trygvis/Quansheng_UV-K5_Wiki/frog-5030712_640.png

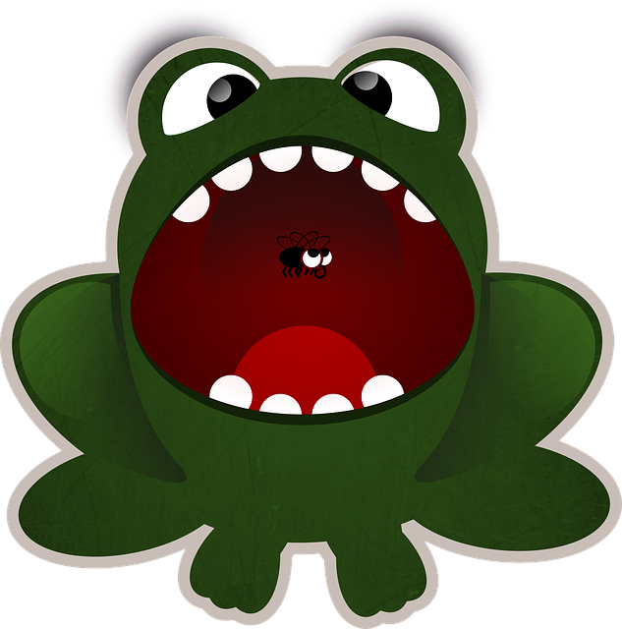
frog-5030712_640.png
