trygvis/Quansheng_UV-K5_Wiki/hardware/Empty_PCB_V1.4/PCB_1.4_FS_2023-09-14 15.27.33.jpg

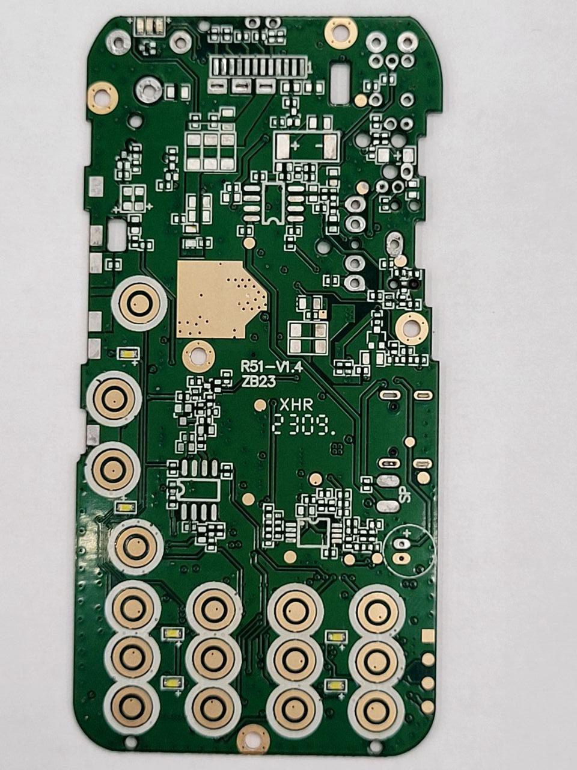
hardware/Empty_PCB_V1.4/PCB_1.4_FS_2023-09-14 15.27.33.jpg
