trygvis/Quansheng_UV-K5_Wiki/hardware/X-Ray/sloping/bok2-5.jpg

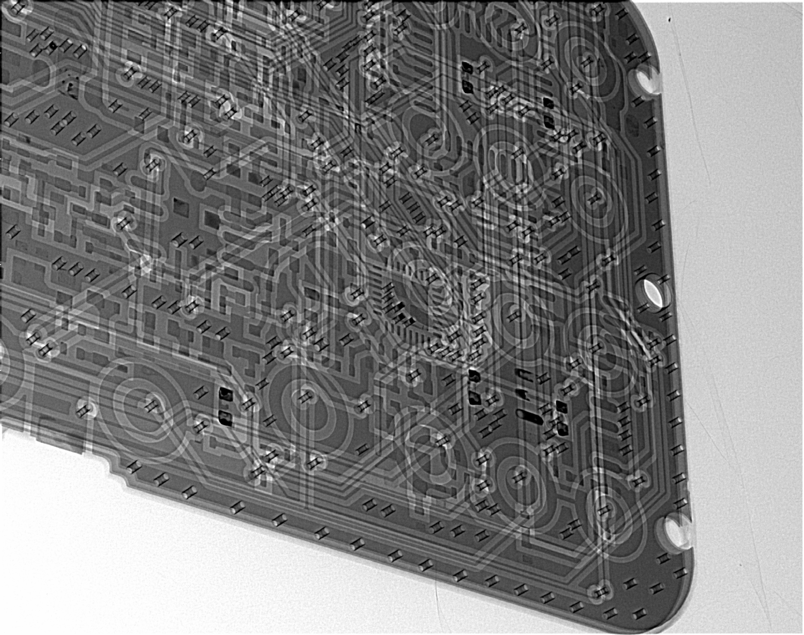
hardware/X-Ray/sloping/bok2-5.jpg
