trygvis/Quansheng_UV-K5_Wiki/hardware/X-Ray/sloping/bok2.jpg

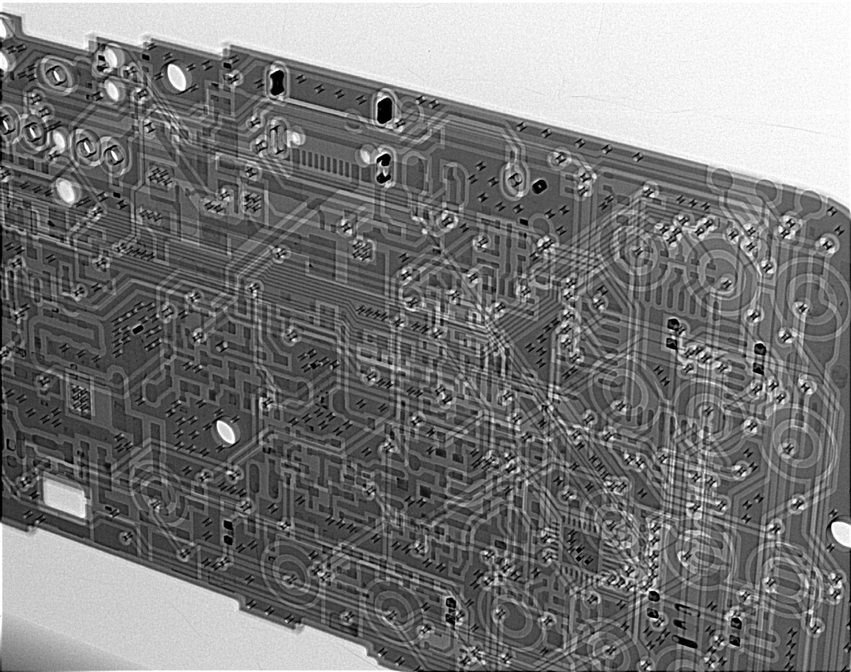
hardware/X-Ray/sloping/bok2.jpg
