trygvis/Quansheng_UV-K5_Wiki/hardware/X-Ray/sloping/bok3.jpg

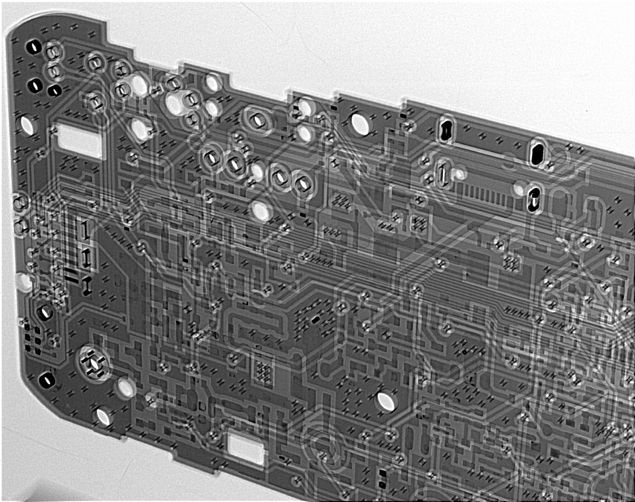
hardware/X-Ray/sloping/bok3.jpg
