trygvis/Quansheng_UV-K5_Wiki/hardware/X-Ray/sloping/bokv2-1.jpg

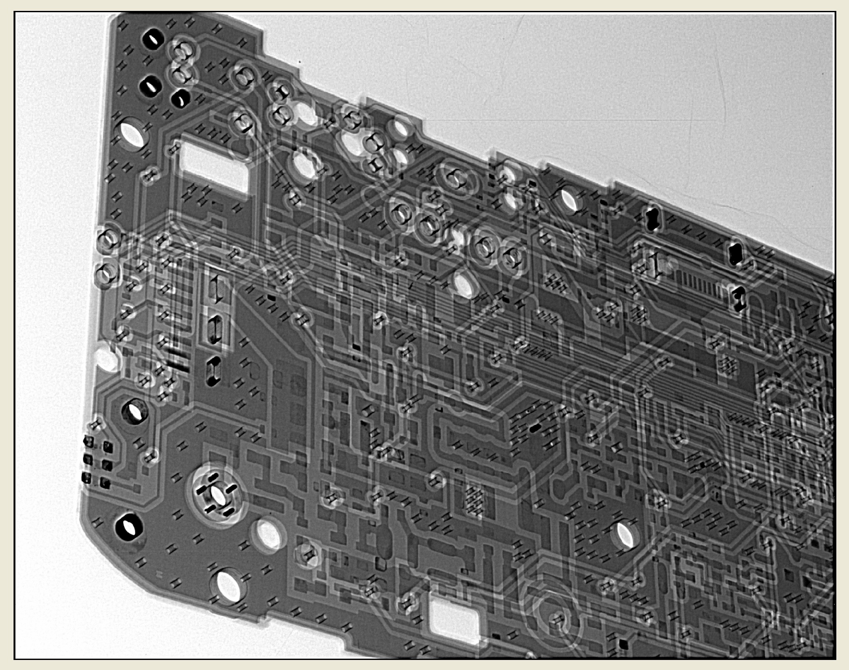
hardware/X-Ray/sloping/bokv2-1.jpg
