trygvis/Quansheng_UV-K5_Wiki/hardware/X-Ray/XRay_RU1_2023-09-13.jpg

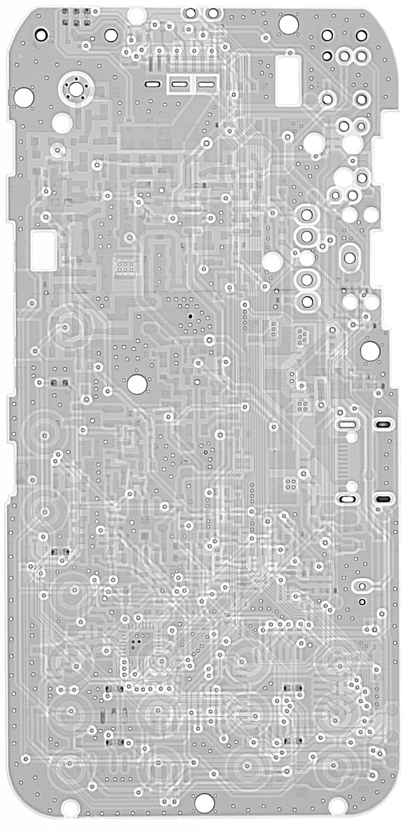
hardware/X-Ray/XRay_RU1_2023-09-13.jpg
