trygvis/Quansheng_UV-K5_Wiki/Manual/Custom_Bootloader_with_Multiple_Firmwares_on_Quansheng_UV_K5_UV.pdf

## Custom Bootloader with Multiple Firmwares on Quansheng UV-K5 UV-K6

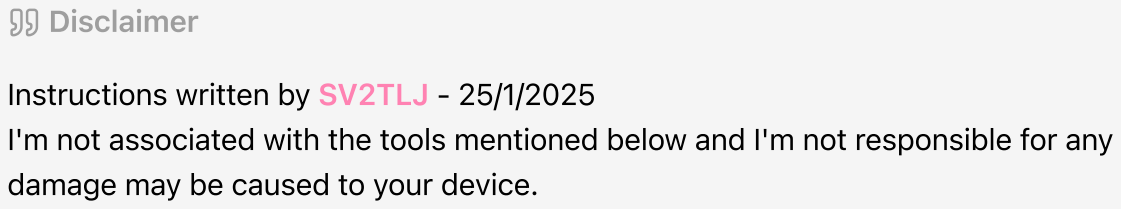
[picture p77: figure]
Disclaimer; damage may be caused to your device.

This method allows us to store up to 4 firmwares in EEPROM and select which one to flash on the go. The selection is done through a list menu and allows us to switch between firmwares without a computer.

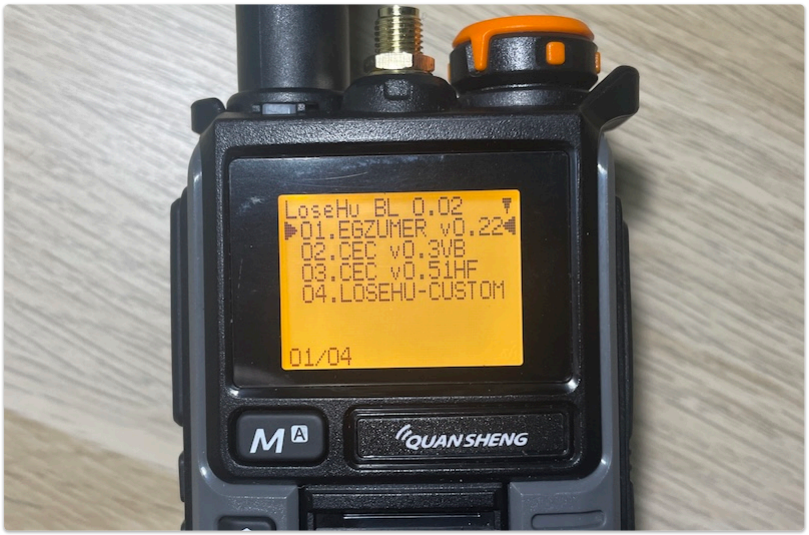
[picture p78: figure]

You will need:

Instructions written by SV2TLJ - 25/1/2025
I'm not associated with the tools mentioned below and I'm not responsible for any

2x 2Mib EEPROM chips (M24M02, AT24CM02, BL24CM02A) Soldering Iron
ST-Link and four wires with female Dupont
Chrome based browser

## Install EEPROM

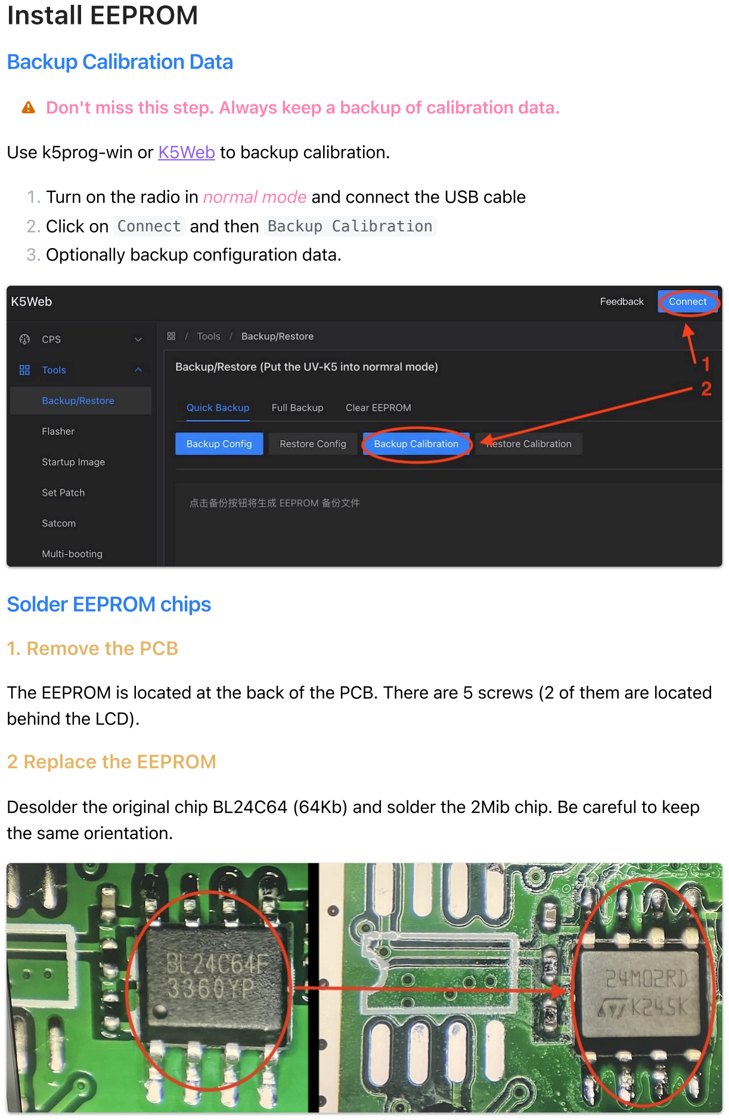
[picture p79: page 2]

Backup Calibration Data

Use k5prog-win or K5Web (https://k5.vicicode.com/#/tool/backup) to backup calibration.

Solder EEPROM chips

1. Remove the PCB

The EEPROM is located at the back of the PCB. There are 5 screws (2 of them are located behind the LCD).

2 Replace the EEPROM

Desolder the original chip BL24C64 (64Kb) and solder the 2Mib chip. Be careful to keep the same orientation.

Don't miss this step. Always keep a backup of calibration data.

1. Turn on the radio in normal mode and connect the USB cable
2. Click on Connect and then Backup Calibration
3. Optionally backup configuration data.

3. Add the second EEPROM

The radio I modded is a UV-K5(99) and it came with a PCB version R51-V1.8. On this PCB there is already a populated footprint for another EEPROM.

For other PCB versions:
If there is not a location to solder the 2nd chip, you need to solder jumper wires between the two chips. Connect all the pads of the two chips in parallel (pad 1 to pad1, pad 2 to pad 2 e.t.c), except pad 3.
Pad 3 on the 1st EEPROM is connected to ground. Pad 3 on the 2nd EEPROM should be pulled up to Vcc. Put a jumper or a 10K resistor between pad 3 and pad 8 on the 2nd chip.

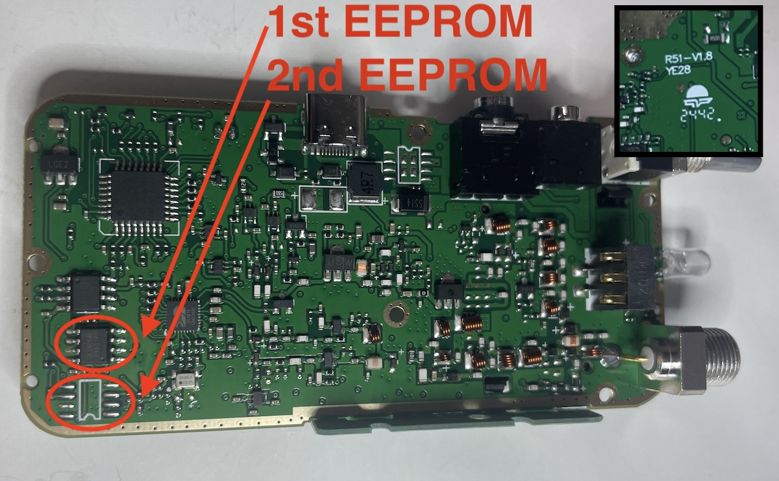
[picture p80: figure]

## Bootloader with multiple firmwares

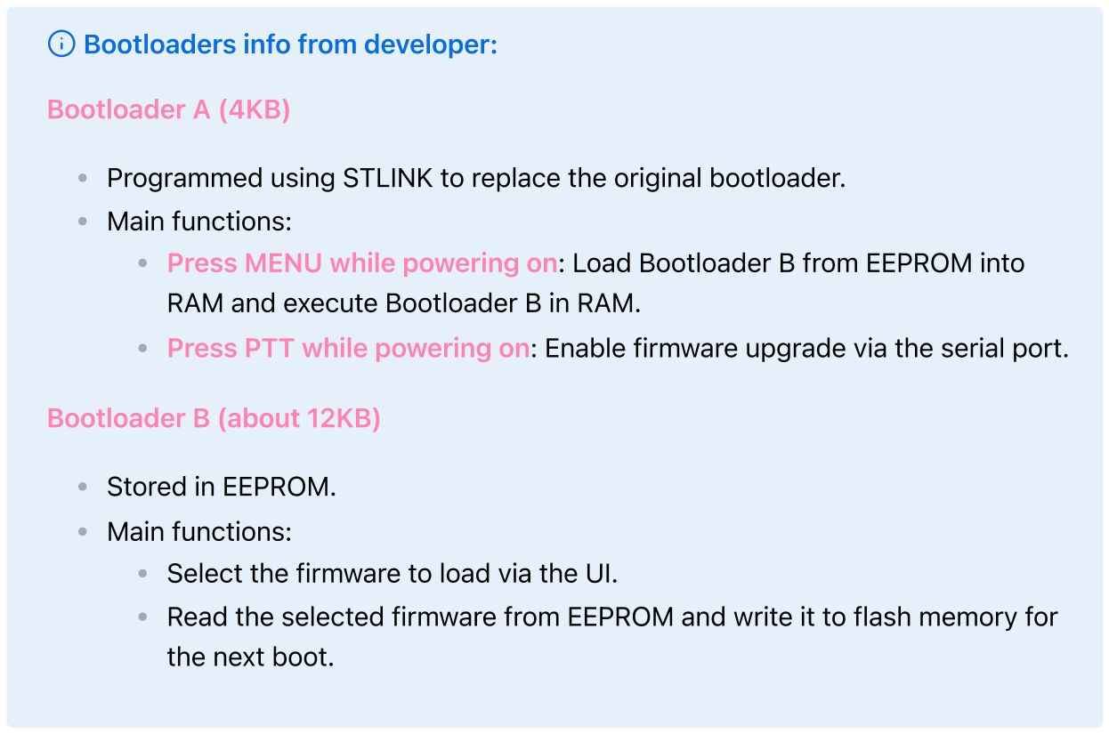
[picture p81: figure]
Bootloaders info from developer:; Bootloader A (4KB); Bootloader B (about 12KB); Main functions:; RAM and execute Bootloader B in RAM.; Stored in EEPROM. Main functions: Select the firmware to load via the UI.; the next boot.

1. Flash the losehu firmware

Go to LOSEHU DIY (https://k5.vicicode.com/#/idea/losehu) and select the Chinese Channel Name . This firmware requires a 4Mib EEPROM installed and its name ends with 400000000 .

Programmed using STLINK to replace the original bootloader.

Press MENU while powering on: Load Bootloader B from EEPROM into

Press PTT while powering on: Enable firmware upgrade via the serial port.

Read the selected firmware from EEPROM and write it to flash memory for

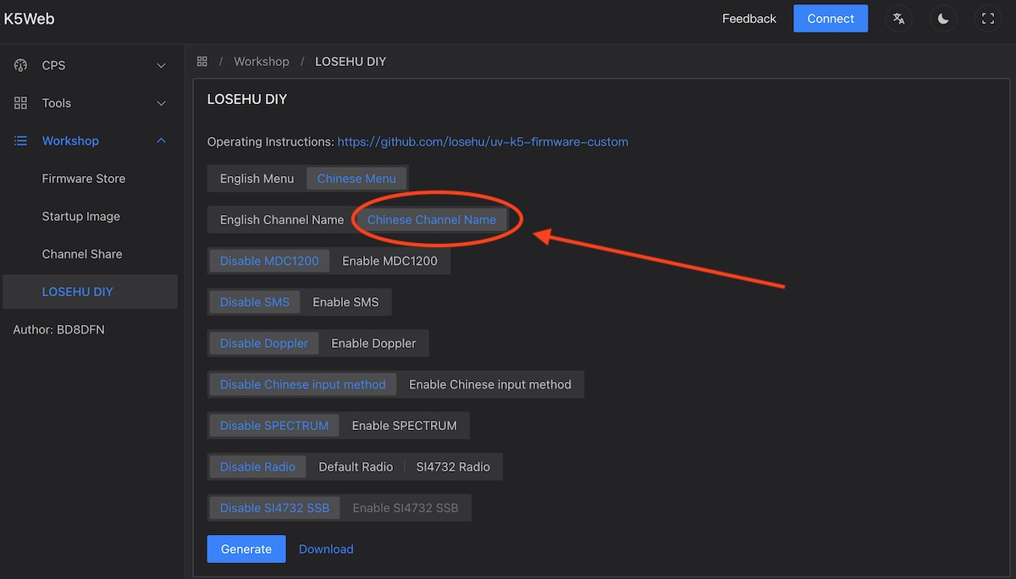
[picture p82: figure]
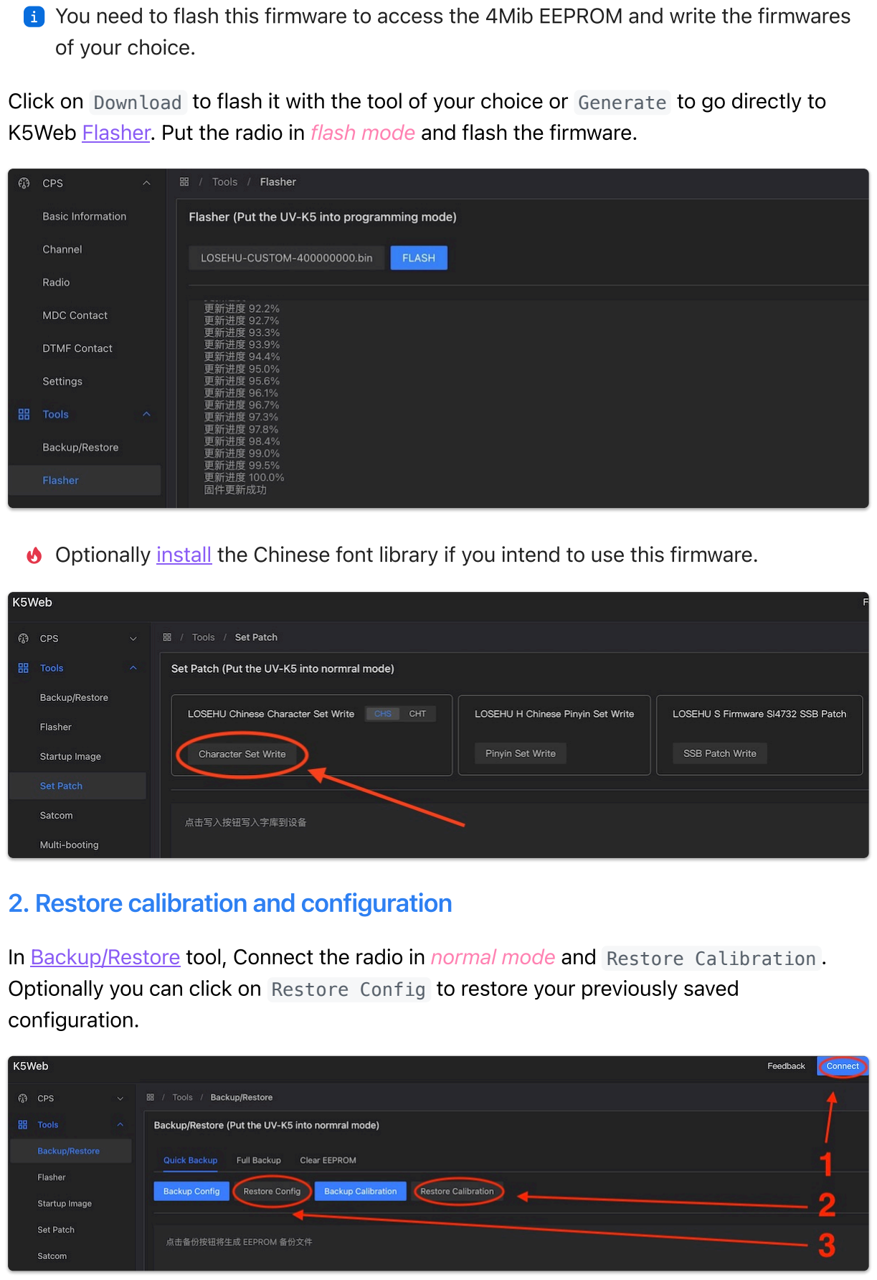
[picture p83: page 5]

Click on Download to flash it with the tool of your choice or Generate to go directly to K5Web Flasher. (https://k5.vicicode.com/#/tool/flash) Put the radio in flash mode and flash the firmware.

2. Restore calibration and configuration

In Backup/Restore (https://k5.vicicode.com/#/tool/backup) tool, Connect the radio in normal mode and Restore Calibration . Optionally you can click on Restore Config to restore your previously saved configuration.

You need to flash this firmware to access the 4Mib EEPROM and write the firmwares of your choice.

Optionally install (https://k5.vicicode.com/#/tool/chi) the Chinese font library if you intend to use this firmware.

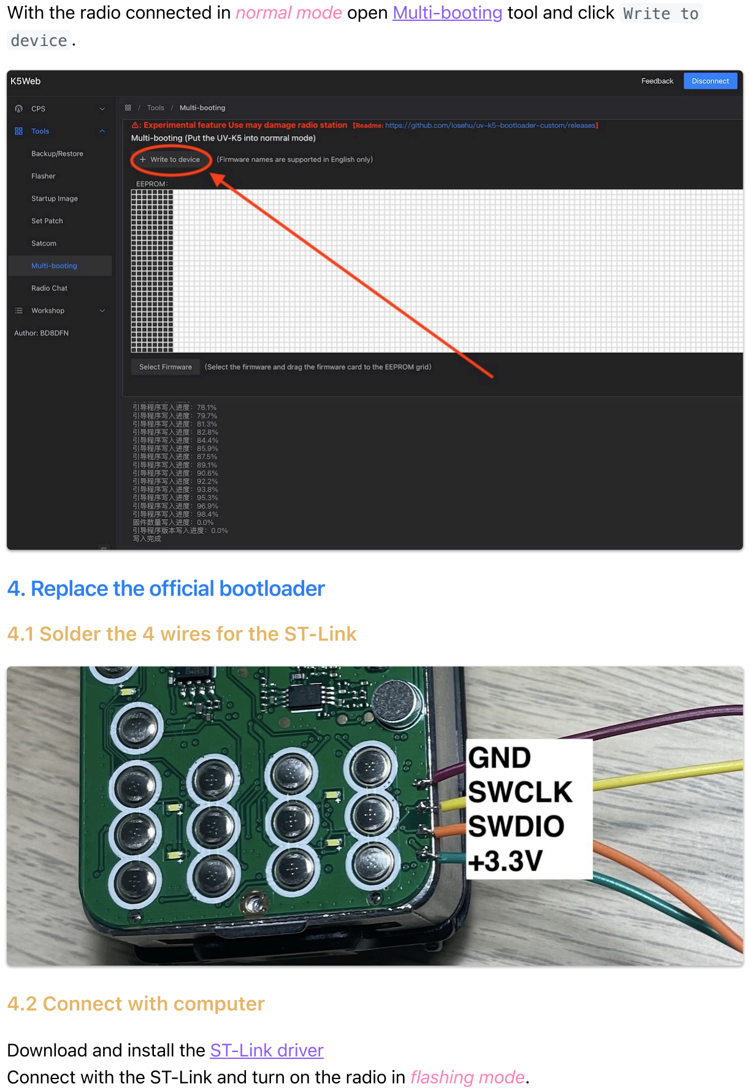
[picture p84: page 6]

With the radio connected in normal mode open Multi-booting (https://k5.vicicode.com/#/tool/bl) tool and click Write to
device .
4. Replace the official bootloader

4.1 Solder the 4 wires for the ST-Link

4.2 Connect with computer

Download and install the ST-Link driver (https://www.st.com/en/development-tools/stsw-link009.html)
Connect with the ST-Link and turn on the radio in flashing mode.

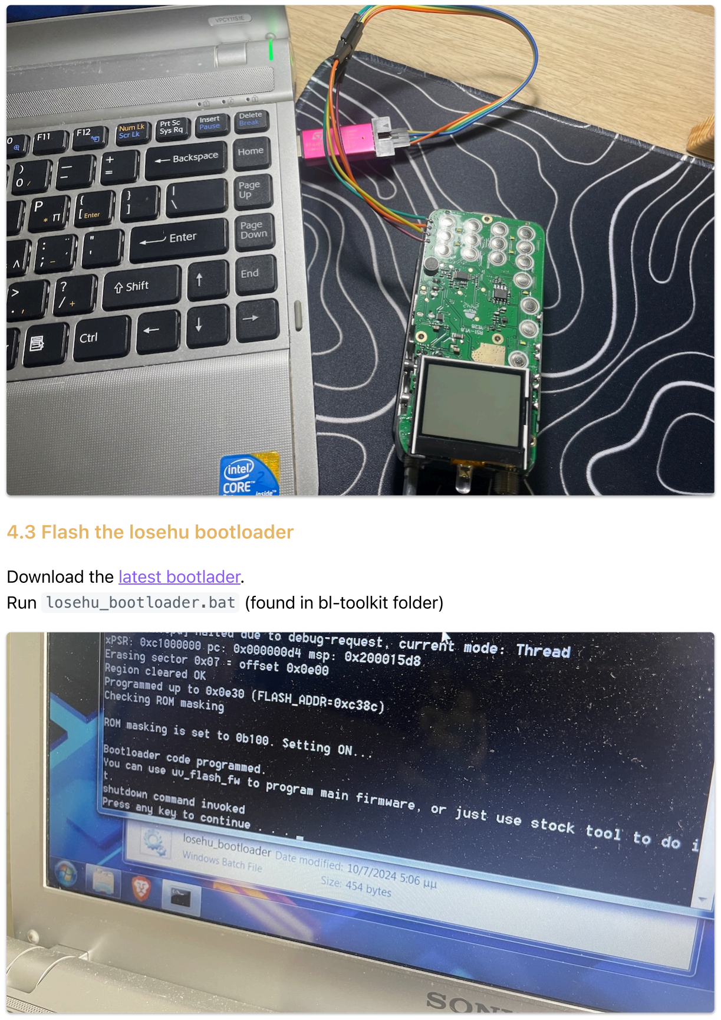
[picture p85: page 7]

4.3 Flash the losehu bootloader

Download the latest bootlader. (https://github.com/losehu/uv-k5-bootloader-custom/releases)
Run losehu_bootloader.bat (found in bl-toolkit folder)

5. Write firmware in EEPROM

Use Multi-booting (https://k5.vicicode.com/#/tool/bl) tool with the radio connected in normal mode.
Click Select Firmare and open the firmwares you want to write (up to 4 files). Drag each one on the first white square.
Click Write to device to write all of them.

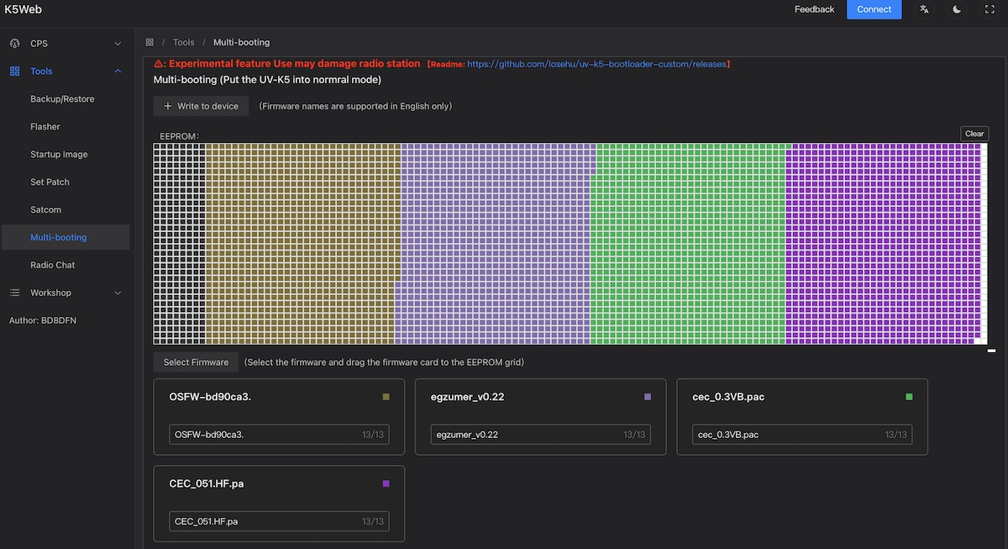
[picture p86: figure]

6. Testflashing using EEPROM

Turn on the radio with the Menu button pressed. You should see a list of the installed firmwares in EEPROM. Select you choice with the arrows and use the Menu button to start flashing. If it stucks for a while and it's not rebooting you might have forgotten to restore the calibration data.

You need to have losehu firmware flashed to use K5Web Multi-Booting tool.

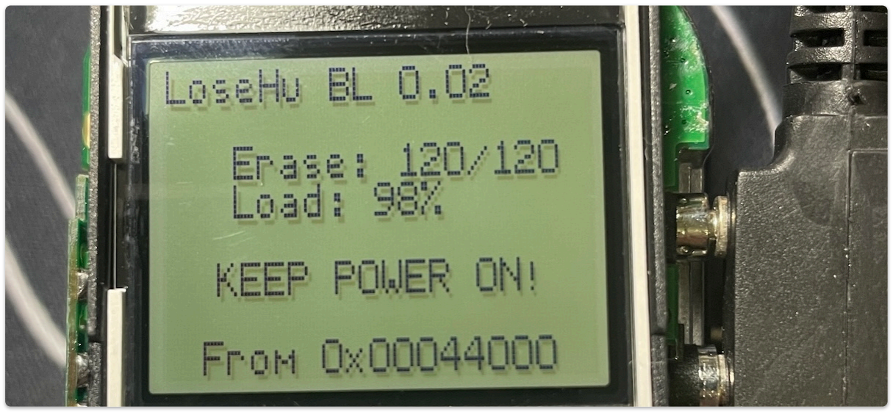
[picture p87: figure]

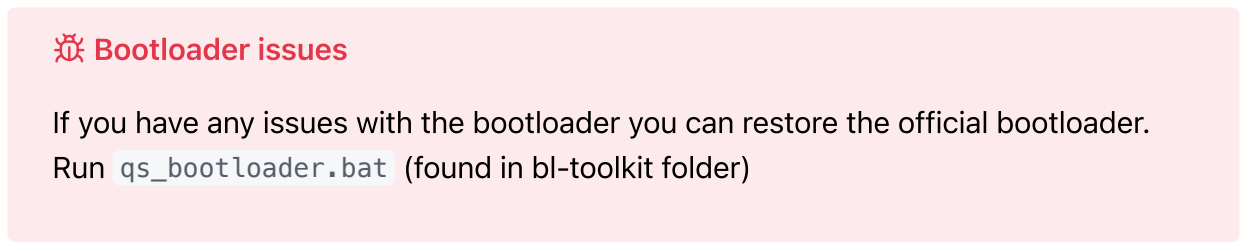
[picture p88: figure]
Bootloader issues

## Useful links

losehu uv-k5-firmware-custom (https://github.com/losehu/uv-k5-firmware-custom) - README en (https://github.com/losehu/uv-k5-firmware-custom/blob/main/README_en.md)
losehu uv-k5-bootloader-custom (https://github.com/losehu/uv-k5-bootloader-custom) - README en (https://github.com/losehu/uv-k5-bootloader-custom/blob/main/README_en.md) - Instructions (https://github.com/losehu/uv-k5-bootloader-custom/blob/main/Losehu%20Bootloader%E8%AF%B4%E6%98%8E%E4%B9%A6.pdf) in Chinese

Tools:

If you have any issues with the bootloader you can restore the official bootloader. Run qs_bootloader.bat (found in bl-toolkit folder)

K5Web (https://k5.vicicode.com/#/chirp/base)
k5prog-win (https://github.com/OneOfEleven/k5prog-win)
