trygvis/Quansheng_UV-K5_Wiki/hardware/Block_Diagram/Quansheng_UV-K5_Block_Diagram_v01.drawio.pdf

~

~~

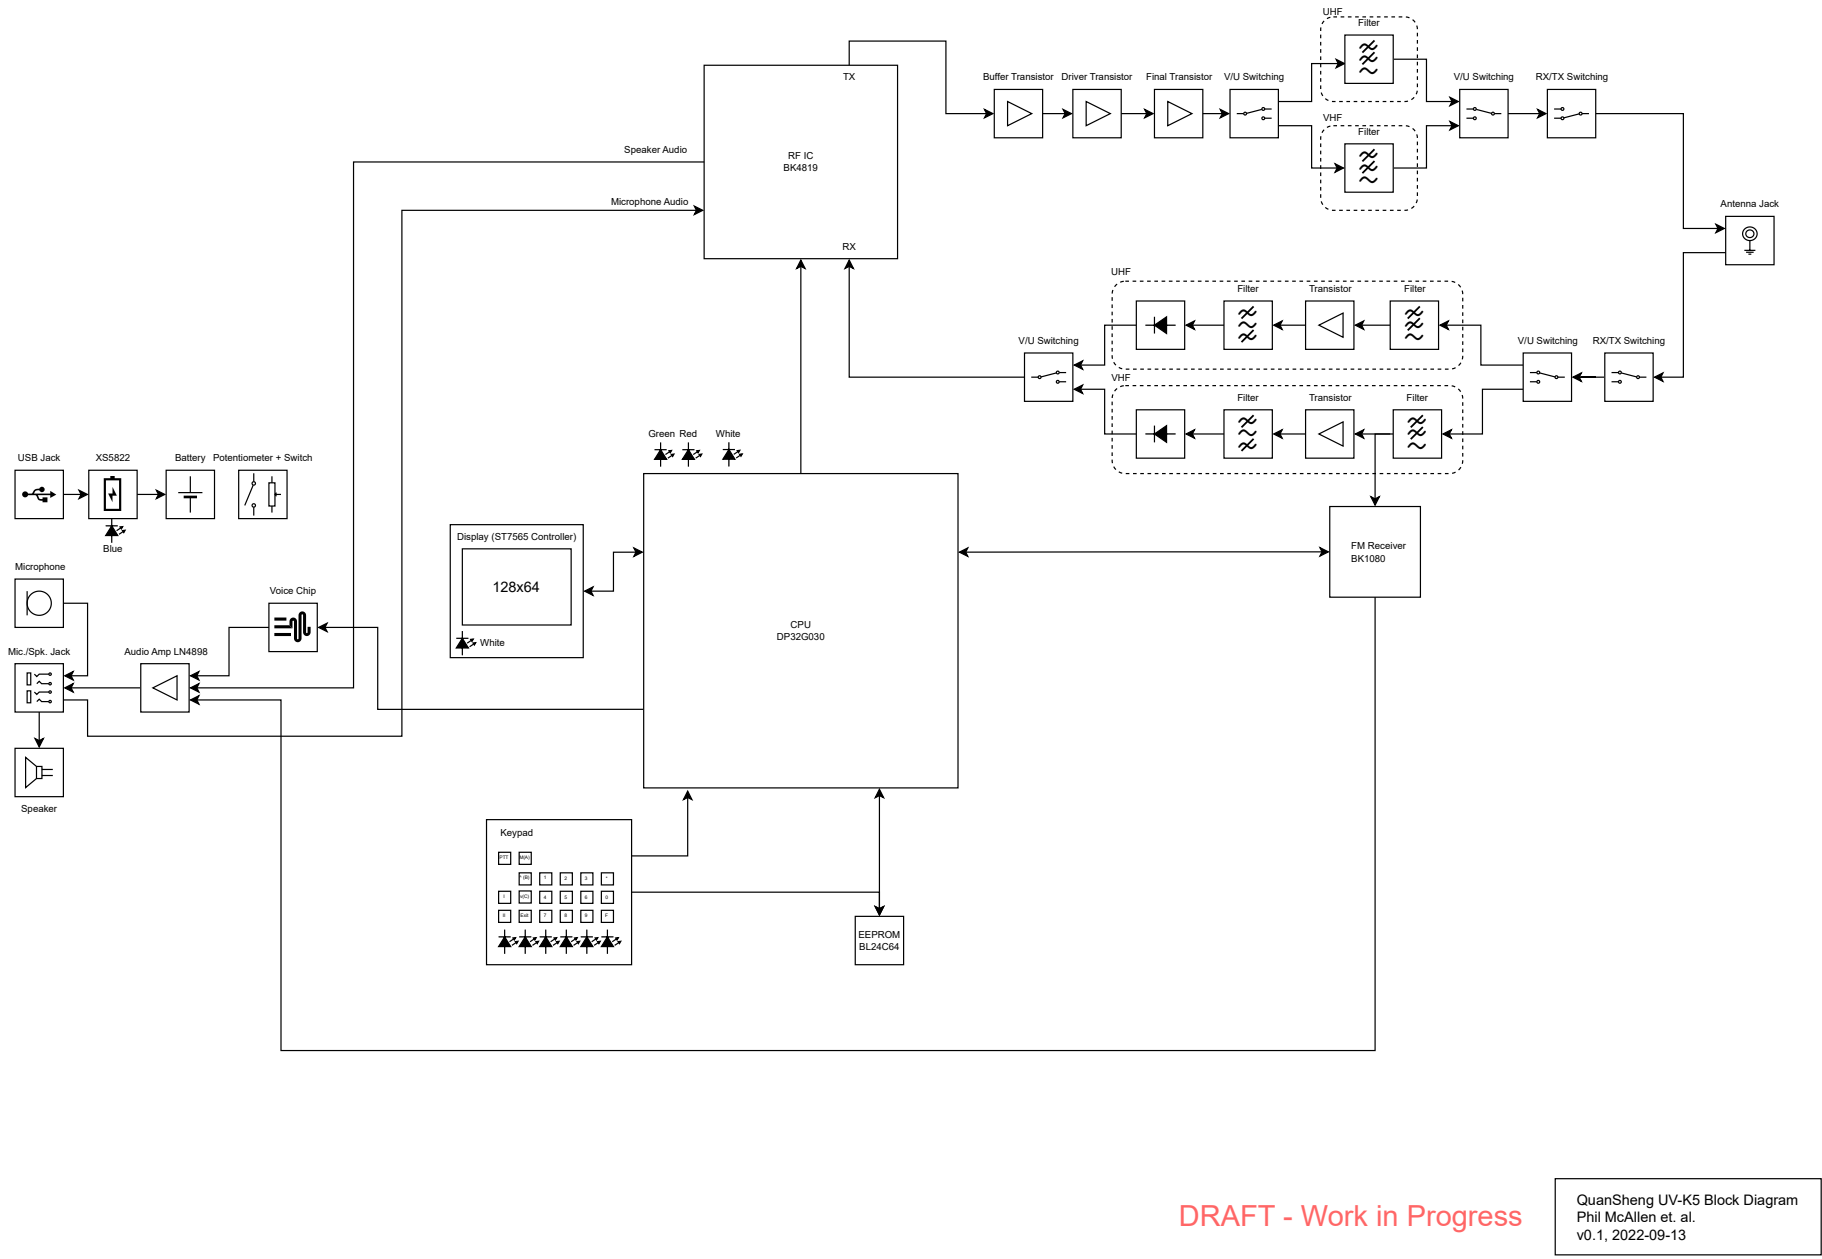
[picture p89: page 1]
Speaker; Antenna Jack; CPU DP32G030; Audio Amp LN4898; Microphone; USB Jack; Keypad; FM Receiver BK1080; EEPROM BL24C64; Voice Chip; Battery; Display (ST7565 Controller); White; Transistor; Buffer Transistor Driver Transistor; Final Transistor; UHF; VHF; V/U Switching; Microphone Audio; Speaker Audio; RX/TX Switching; Potentiometer + Switch; Filter ~~; Filter ~; PTT; Exit; Blue; Green Red; Filter

RX/TX Switching

Mic./Spk. Jack

QuanSheng UV-K5 Block Diagram
Phil McAllen et. al.

DRAFT - Work in Progress
