trygvis/Quansheng_UV-K5_Wiki/hardware/KiCad/UVK5_reversing-70MHz_modv_20230702.pdf

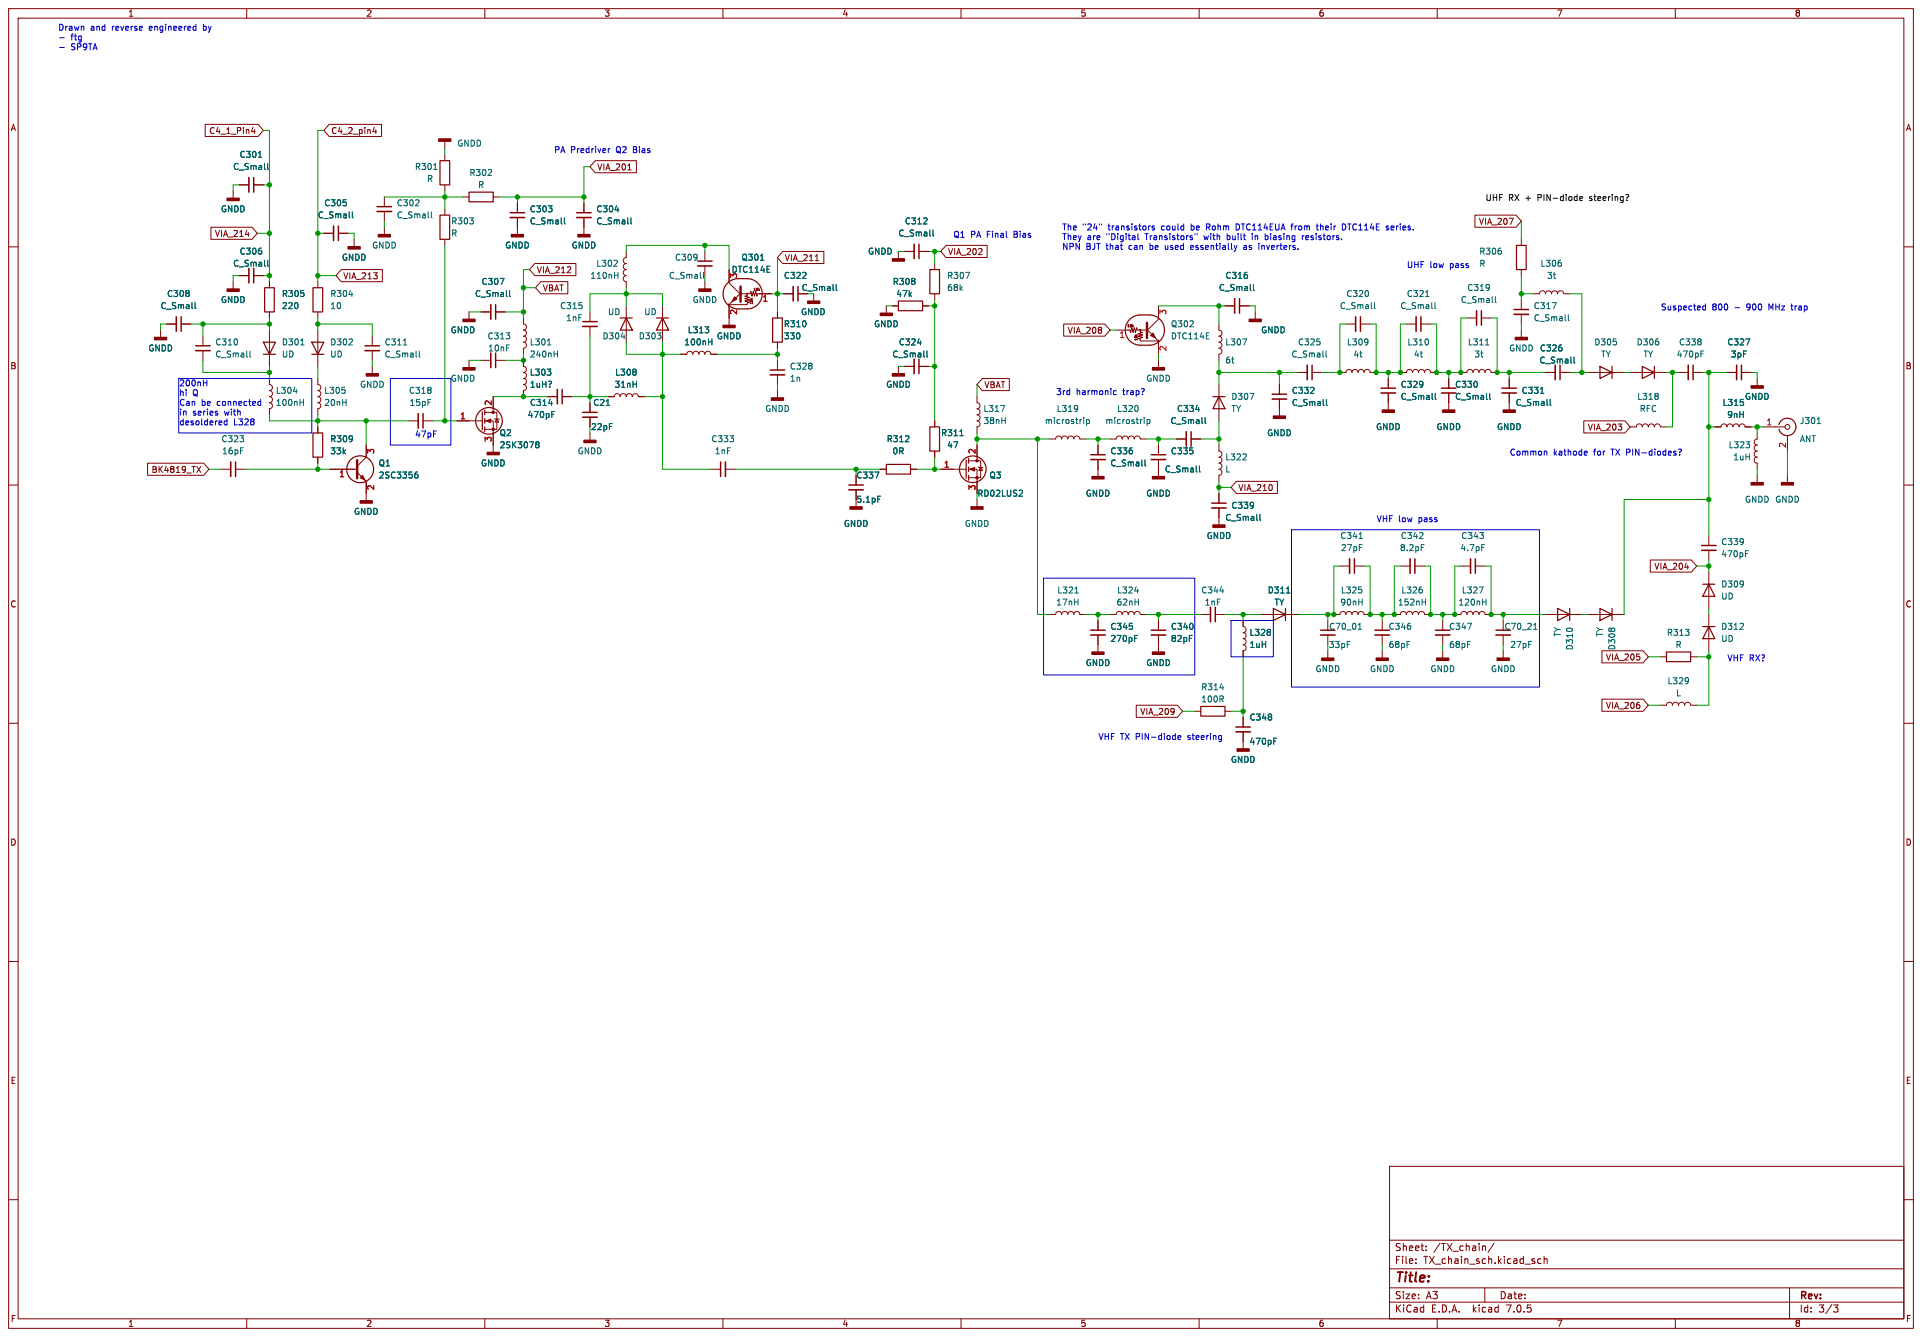
[picture p90: page 1]

Id: 3/3 Title: File: TX_chain_sch.kicad_sch Sheet: /TX_chain/
