trygvis/Quansheng_UV-K5_Wiki/hardware/KiCad/UVK5_reversing_06-02-2024/CPU.kicad_sch

## KiCad design hardware/KiCad/UVK5_reversing_06-02-2024/CPU.kicad_sch (2024-02-06)

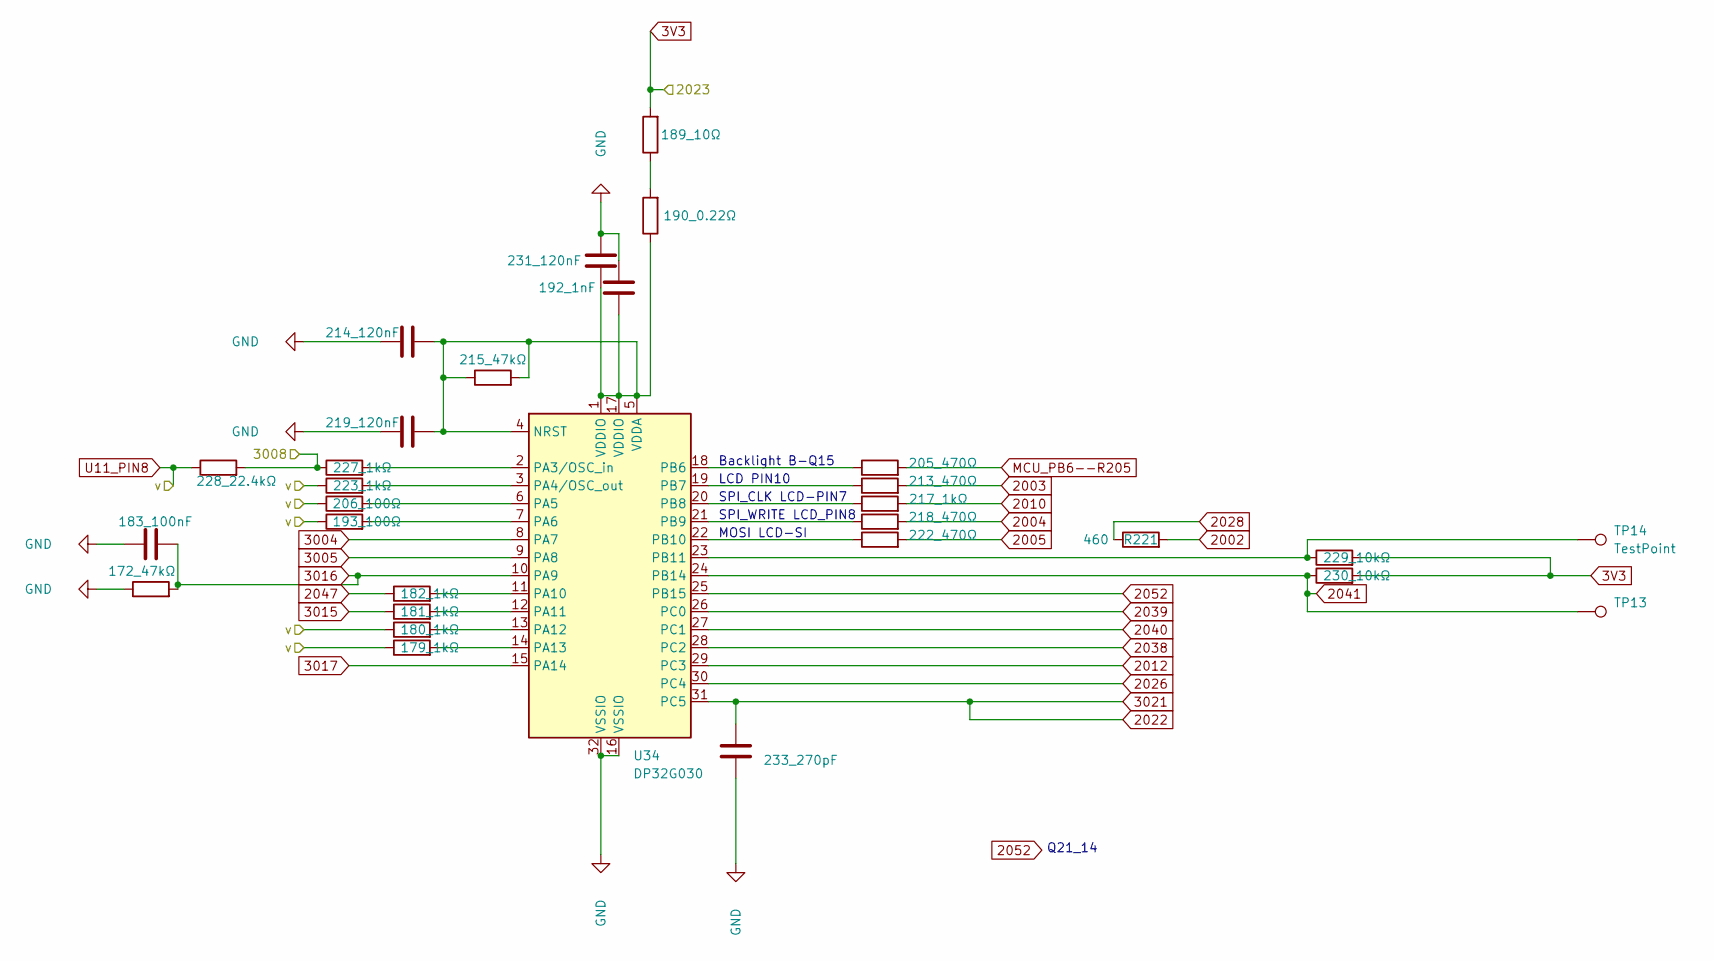
[picture p91: schematic CPU.kicad_sch]

Parts:
C94: 192_1nF
C126: 219_120nF
C183: 183_100nF
C214: 214_120nF
C231: 231_120nF
C233: 233_270pF
R91: 190_0.22Ω
R92: 189_10Ω
R95: 215_47kΩ
R96: 228_22.4kΩ
R97: 180_1kΩ
R100: 179_1kΩ
R172: 172_47kΩ
R181: 181_1kΩ
R182: 182_1kΩ
R193: 193_100Ω
R205: 205_470Ω
R206: 206_100Ω
R213: 213_470Ω
R217: 217_1kΩ
R218: 218_470Ω
R221: 460
R222: 222_470Ω
R223: 223_1kΩ
R227: 227_1kΩ
R229: 229_10kΩ
R230: 230_10kΩ
TP13, TP14: TestPoint
U34: DP32G030; LQFP-32_7x7mm_P0.8mm

Connections:
3V3: R92.2, R229.2, R230.2
2002: R221.2
2003: R213.2
2004: R218.2
2005: R222.2
2010: R217.2
2012: U34.29 (PC3)
2022: C233.2, U34.31 (PC5)
2026: U34.30 (PC4)
2028: R221.1
2038: U34.28 (PC2)
2039: U34.26 (PC0)
2040: U34.27 (PC1)
2041: R230.1, TP13.1, U34.24 (PB14)
2047: R182.1
2052: U34.25 (PB15)
3004: U34.8 (PA7)
3005: U34.9 (PA8)
3008: R96.2, R227.1
3015: R181.1
3016: C183.2, R172.2, U34.10 (PA9)
3017: U34.15 (PA14)
GND: C94.1, C126.1, C183.1, C214.1, C231.1, C233.1, R172.1, U34.16 (VSSIO), U34.32 (VSS)
MCU_PB6--R205: R205.2
unnamed: C94.2, C126.2, C214.2, C231.2, R91.1, R95.1, R95.2, U34.1 (VDDIO), U34.4 (NRST), U34.5 (VDDA), U34.17 (VDDIO)
unnamed: R91.2, R92.1
unnamed: R97.2, U34.13 (PA12)
unnamed: R100.2, U34.14 (PA13)
unnamed: R181.2, U34.12 (PA11)
unnamed: R182.2, U34.11 (PA10)
unnamed: R193.2, U34.7 (PA6)
unnamed: R205.1, U34.18 (PB6)
unnamed: R206.2, U34.6 (PA5)
unnamed: R213.1, U34.19 (PB7)
unnamed: R217.1, U34.20 (PB8)
unnamed: R218.1, U34.21 (PB9)
unnamed: R222.1, U34.22 (PB10)
unnamed: R223.2, U34.3 (PA4/OSC_out)
unnamed: R227.2, U34.2 (PA3/OSC_in)
unnamed: R229.1, TP14.1, U34.23 (PB11)
U11_PIN8: R96.1, R97.1, R100.1, R193.1, R206.1, R223.1

Notes on the sheet:
Q21_14
MOSI LCD-SI
Backlight B-Q15
SPI_WRITE LCD_PIN8
LCD PIN10
SPI_CLK LCD-PIN7
