trygvis/Quansheng_UV-K5_Wiki/hardware/KiCad/UVK5_reversing_06-02-2024/Charger.kicad_sch

## KiCad design hardware/KiCad/UVK5_reversing_06-02-2024/Charger.kicad_sch (2025-08-14, an earlier design)

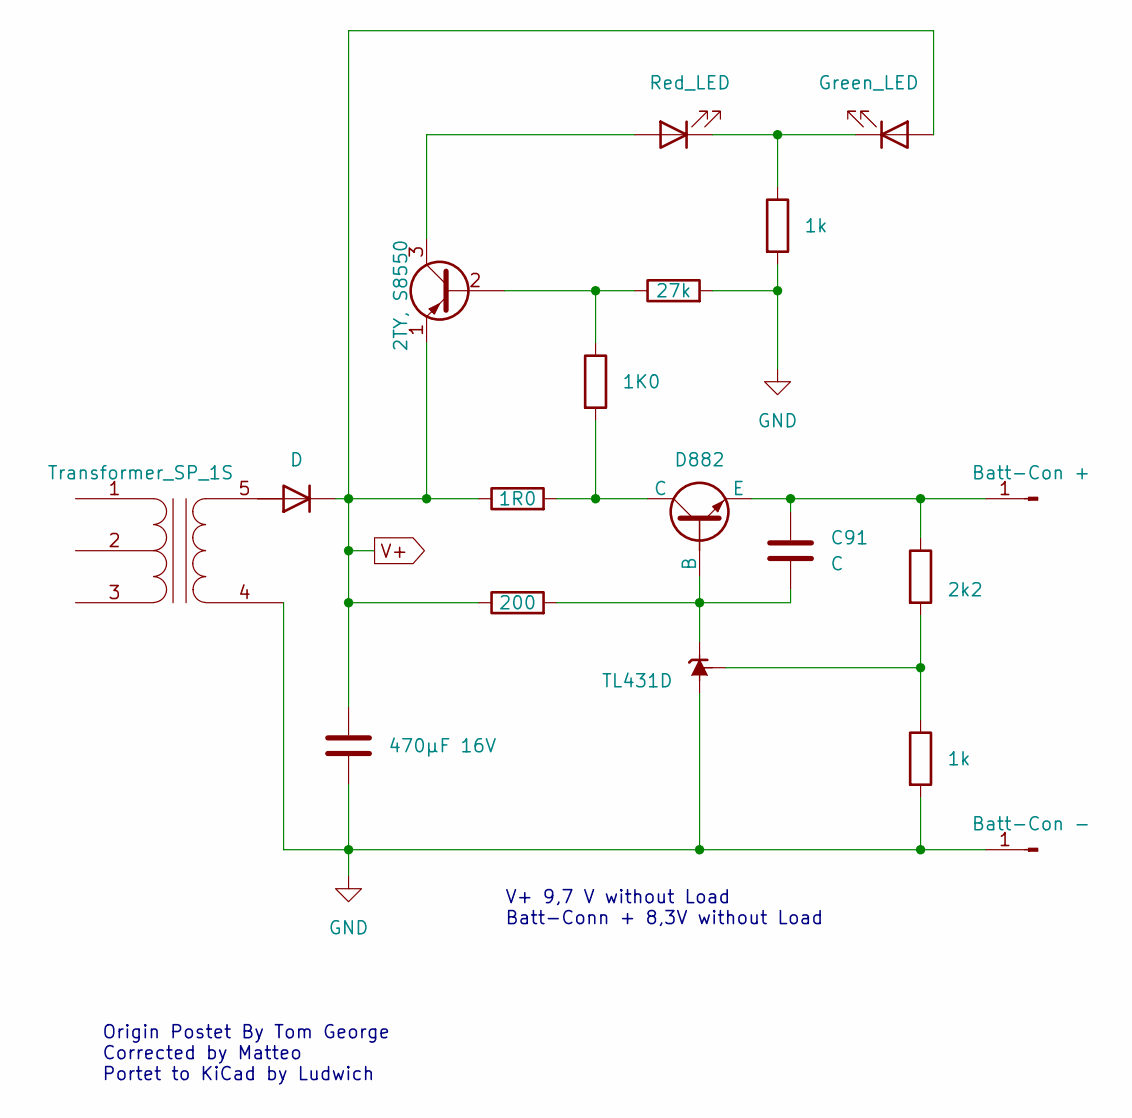
[picture p92: schematic Charger.kicad_sch]

Parts:
C91: C
C92: 470µF 16V
D41: Red_LED
D42: Green_LED
D43: D
J27: Batt-Con +
J28: Batt-Con -
Q30: 2TY, S8550
Q31: D882
R52, R58: 1k
R53: 27k
R55: 1R0
R56: 2k2
R57: 200
T21: Transformer_SP_1S
U23: TL431D; SOIC-8_3.9x4.9mm_P1.27mm
r54: 1K0

Connections:
GND: C92.2, J28.1, R52.2, R53.2, R58.2, T21.4 (S1), U23.2 (A), U23.3 (A), U23.6 (A), U23.7 (A)
unnamed: C91.1, J27.1, Q31.3 (E), R56.1
unnamed: C91.2, Q31.2 (B), R57.2, U23.1 (K)
unnamed: D41.1 (K), D42.1 (K), R52.1
unnamed: D41.2 (A), Q30.3 (C)
unnamed: Q30.2 (B), R53.1, r54.1
unnamed: Q31.1 (C), R55.2, r54.2
unnamed: R56.2, R58.1, U23.8 (REF)
V+: C92.1, D42.2 (A), D43.1 (K), Q30.1 (E), R55.1, R57.1

Notes on the sheet:
V+ 9,7 V without Load Batt-Conn + 8,3V without Load
Origin Postet By Tom George Corrected by Matteo Portet to KiCad by Ludwich
