trygvis/Quansheng_UV-K5_Wiki/hardware/KiCad/UVK5_reversing_06-02-2024/FM_BK1080.kicad_sch

## KiCad design hardware/KiCad/UVK5_reversing_06-02-2024/FM_BK1080.kicad_sch (2024-02-06)

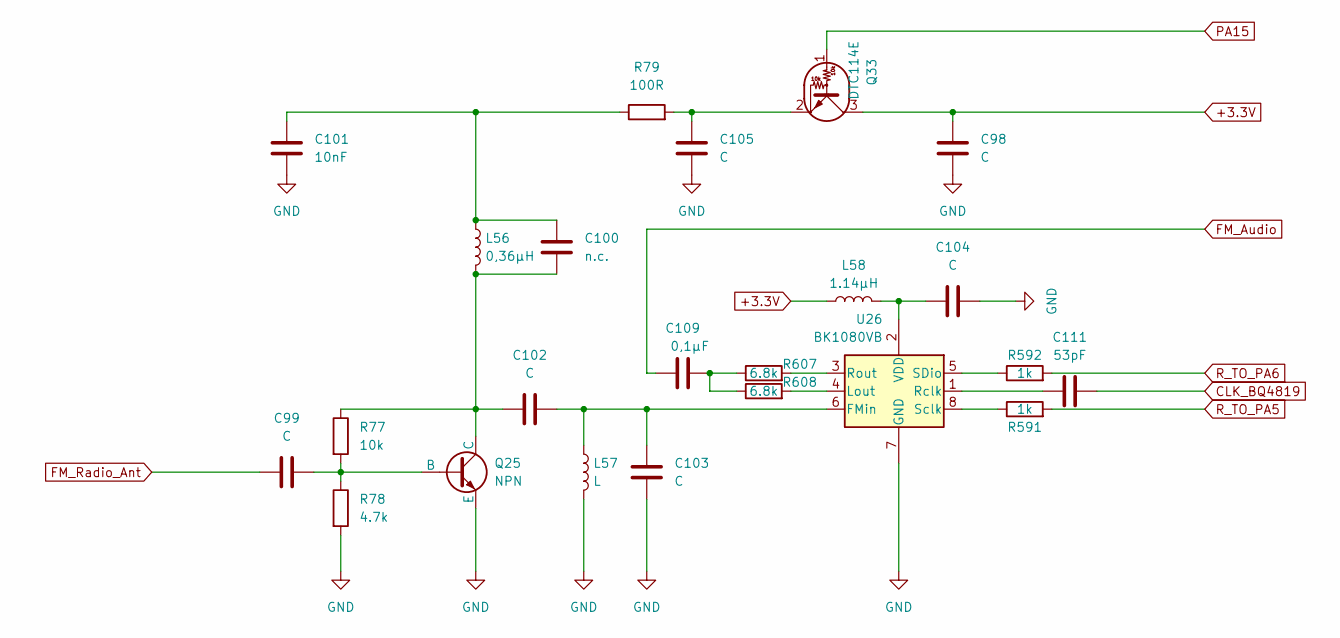
[picture p93: schematic FM_BK1080.kicad_sch]

Parts:
C98, C99, C102, C103, C104, C105: C
C100: n.c.
C101: 10nF
C109: 0,1µF
C111: 53pF
L56: 0,36µH
L57: L
L58: 1.14µH
Q25: NPN
Q33: DTC114E
R77: 10k
R78: 4.7k
R79: 100R
R591, R592: 1k
R607, R608: 6.8k
U26: BK1080VB; SOP-8_3.9x4.9mm_P1.27mm

Connections:
+3.3V: C98.1, L58.1, Q33.3 (C)
CLK_BQ4819: C111.2
FM_Audio: C109.1
FM_Radio_Ant: C99.1
GND: C98.2, C101.2, C103.2, C104.2, C105.2, L57.2, Q25.3 (E), R78.2, U26.7 (GND)
unnamed: C99.2, Q25.2 (B), R77.2, R78.1
unnamed: C100.1, C101.1, L56.1, R79.1
unnamed: C100.2, C102.1, L56.2, Q25.1 (C), R77.1
unnamed: C102.2, C103.1, L57.1, U26.6 (FMin)
unnamed: C104.1, L58.2, U26.2 (VDD)
unnamed: C105.1, Q33.2 (E), R79.2
unnamed: C109.2, R607.1, R608.1
unnamed: C111.1, U26.1 (Rclk)
unnamed: R591.1, U26.8 (Sclk)
unnamed: R592.1, U26.5 (SDio)
unnamed: R607.2, U26.3 (Rout)
unnamed: R608.2, U26.4 (Lout)
PA15: Q33.1 (B)
R_TO_PA5: R591.2
R_TO_PA6: R592.2
