trygvis/Quansheng_UV-K5_Wiki/hardware/KiCad/UVK5_reversing_06-02-2024/Gabiz_ro.kicad_sch

## KiCad design hardware/KiCad/UVK5_reversing_06-02-2024/Gabiz_ro.kicad_sch (2024-02-06)

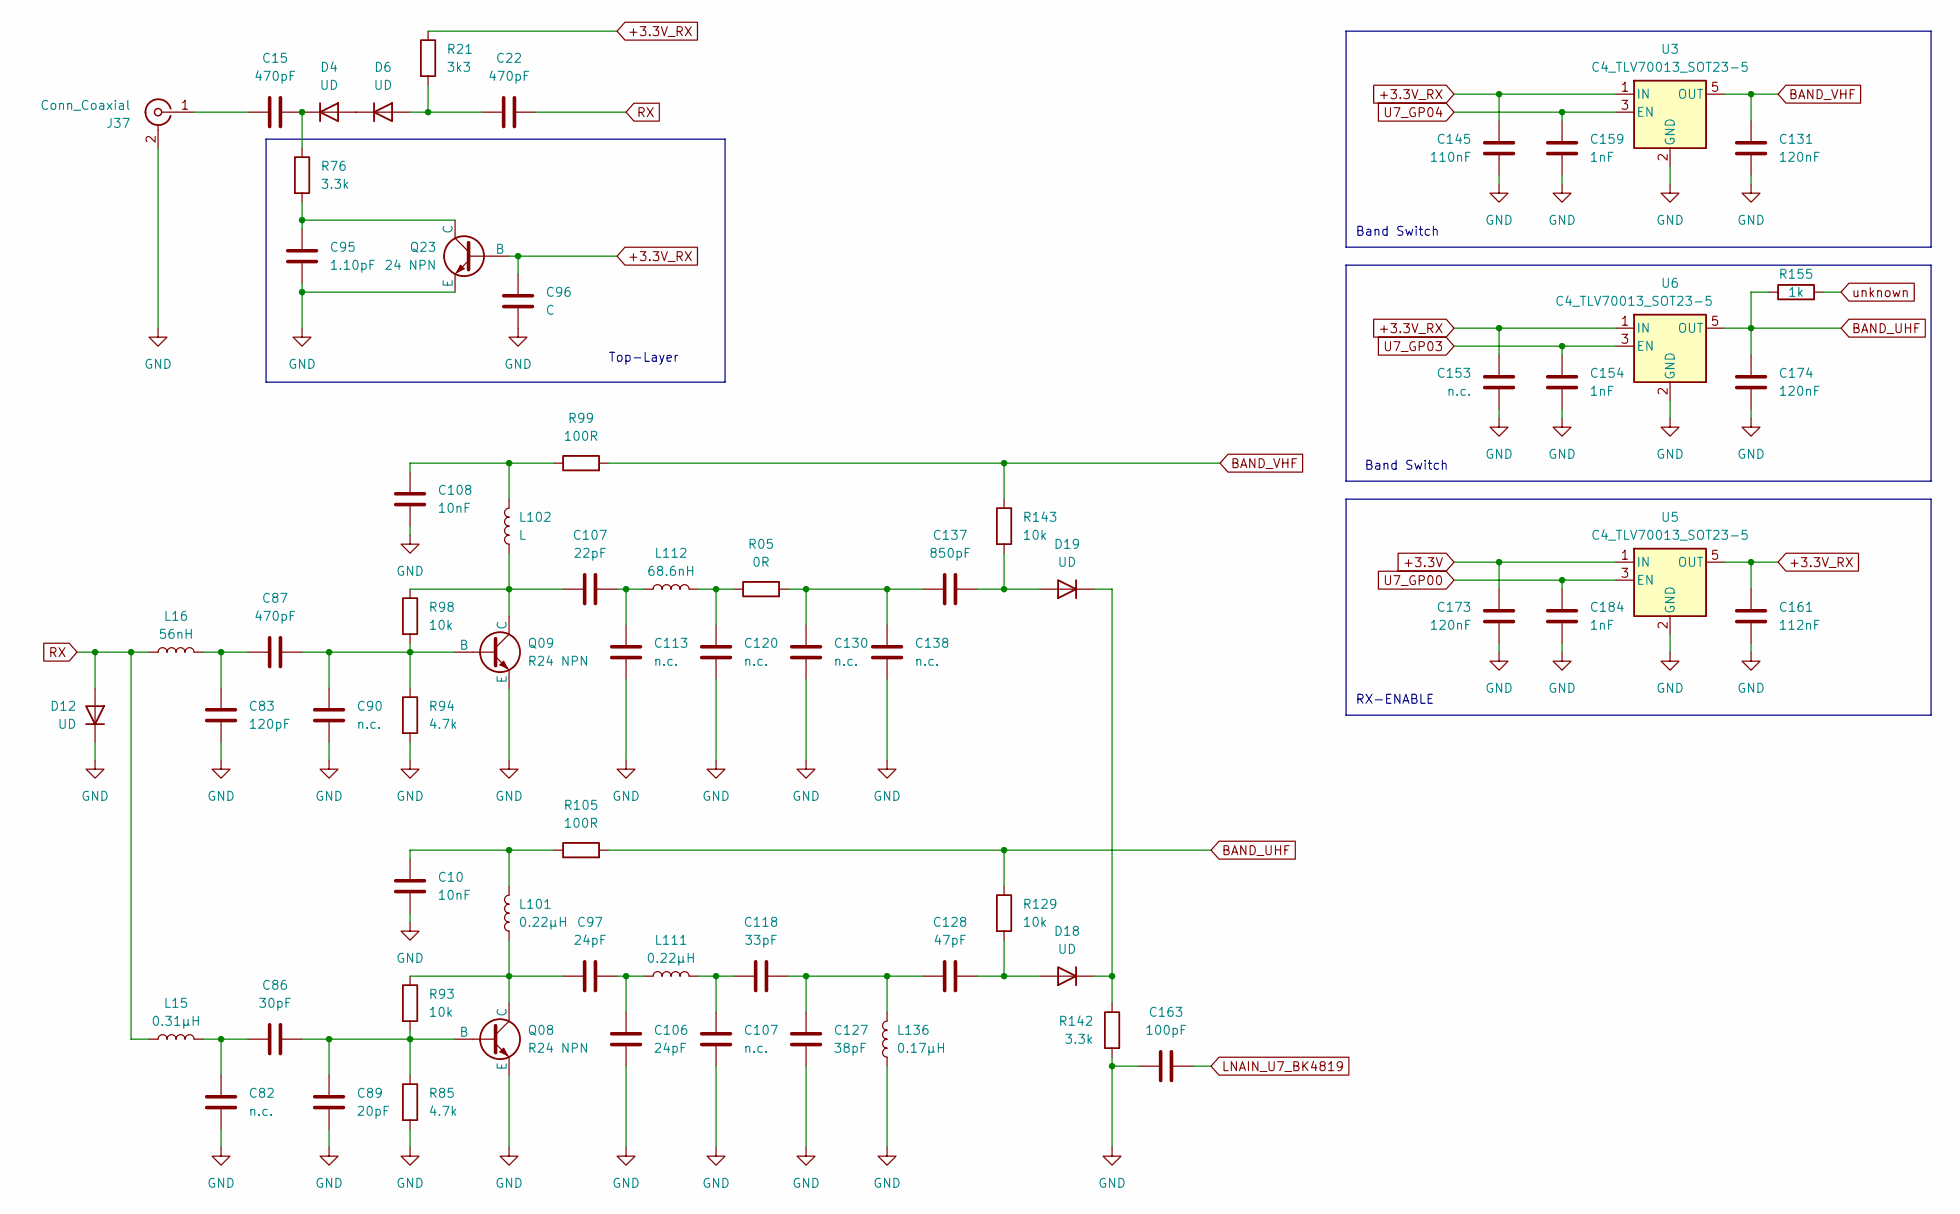
[picture p94: schematic Gabiz_ro.kicad_sch]

Parts:
C10, C108: 10nF
C15, C22, C87: 470pF
C82, C90, C107, C113, C120, C130, C138, C153: n.c.
C83: 120pF
C86: 30pF
C89: 20pF
C95: 1.10pF
C96: C
C97, C106: 24pF
C118: 33pF
C127: 38pF
C128: 47pF
C131, C173, C174: 120nF
C137: 850pF
C145: 110nF
C154, C159, C184: 1nF
C161: 112nF
C163: 100pF
D4, D6, D12, D18, D19: UD
J37: Conn_Coaxial
L15: 0.31µH
L16: 56nH
L101, L111: 0.22µH
L102: L
L112: 68.6nH
L136: 0.17µH
Q08, Q09: R24 NPN
Q23: 24 NPN
R05: 0R
R21: 3k3
R76, R142: 3.3k
R85, R94: 4.7k
R93, R98, R129, R143: 10k
R99, R105: 100R
R155: 1k
U3, U5, U6: C4_TLV70013_SOT23-5; SOT-23-5

Connections:
+3.3V: C173.2, U5.1 (IN)
+3.3V_RX: C96.1, C145.2, C153.2, C161.2, Q23.2 (B), R21.1, U3.1 (IN), U5.5 (OUT), U6.1 (IN)
BAND_UHF: C174.2, R105.2, R129.1, R155.1, U6.5 (OUT)
BAND_VHF: C131.2, R99.2, R143.1, U3.5 (OUT)
GND: C10.2, C82.2, C83.2, C89.2, C90.2, C95.2, C96.2, C106.2, C107.2, C108.2, C113.2, C120.2, C127.2, C130.2, C131.1, C138.2, C145.1, C153.1, C154.1, C159.1, C161.1, C163.1, C173.1, C174.1, C184.1, D12.1 (K), J37.2 (Ext), L136.1, Q08.3 (E), Q09.3 (E), Q23.3 (E), R85.2, R94.2, R142.2, U3.2 (GND), U5.2 (GND), U6.2 (GND)
LNAIN_U7_BK4819: C163.2
unnamed: C10.1, L101.2, R105.1
unnamed: C15.1, J37.1 (In)
unnamed: C15.2, D4.1 (K), R76.1
unnamed: C22.1, D6.2 (A), R21.2
unnamed: C82.1, C86.1, L15.2
unnamed: C83.1, C87.1, L16.2
unnamed: C86.2, C89.1, Q08.2 (B), R85.1, R93.2
unnamed: C87.2, C90.1, Q09.2 (B), R94.1, R98.2
unnamed: C95.1, Q23.1 (C), R76.2
unnamed: C97.1, L101.1, Q08.1 (C), R93.1
unnamed: C97.2, C106.1, L111.1
unnamed: C107.1, C118.1, L102.1, L111.2, Q09.1 (C), R98.1
unnamed: C107.2, C113.1, L112.1
unnamed: C108.1, L102.2, R99.1
unnamed: C118.2, C127.1, C128.1, L136.2
unnamed: C120.1, L112.2, R05.1
unnamed: C128.2, D18.2 (A), R129.2
unnamed: C130.1, C137.1, C138.1, R05.2
unnamed: C137.2, D19.2 (A), R143.2
unnamed: D4.2 (A), D6.1 (K)
unnamed: D18.1 (K), D19.1 (K), R142.1
RX: C22.2, D12.2 (A), L15.1, L16.1
U7_GP00: C184.2, U5.3 (EN)
U7_GP03: C154.2, U6.3 (EN)
U7_GP04: C159.2, U3.3 (EN)
unknown: R155.2

Notes on the sheet:
Band Switch
Top-Layer
RX-ENABLE
