trygvis/Quansheng_UV-K5_Wiki/hardware/KiCad/UVK5_reversing_06-02-2024/K5-Dock.kicad_sch

## KiCad design hardware/KiCad/UVK5_reversing_06-02-2024/K5-Dock.kicad_sch (2024-02-06)

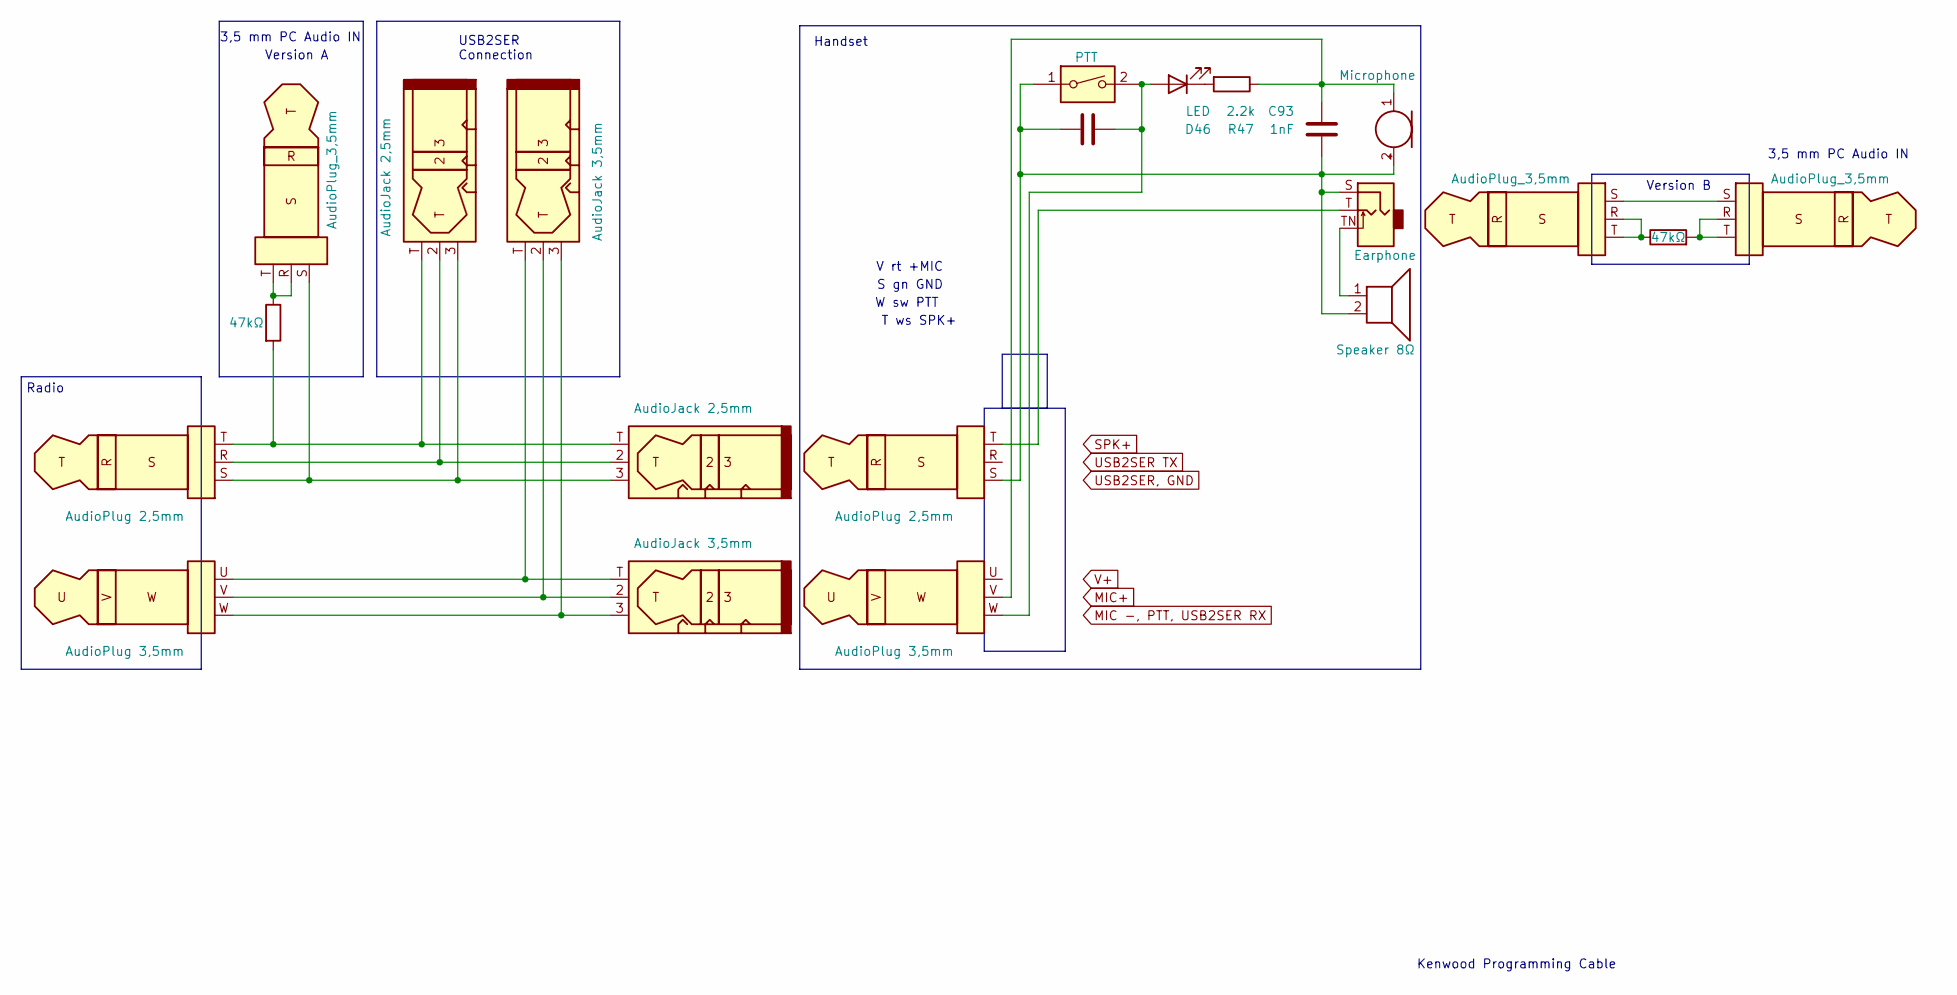
[picture p95: schematic K5-Dock.kicad_sch]

Parts:
2,5mm22, 2,5mm23: AudioPlug 2,5mm
C93, C112: 1nF
D46: LED
J40, J43: AudioJack 2,5mm
J41, J42: AudioJack 3,5mm
J44, J45, J47: AudioPlug_3,5mm
J46, J50: AudioPlug 3,5mm
J52: Earphone
LS24: Speaker 8Ω
MK23: Microphone
R45, R46: 47kΩ
R47: 2.2k
SW41: PTT

Connections:
unnamed: 2,5mm22.S, C93.2, C112.2, J52.S, LS24.2, MK23.2 (+), SW41.1
unnamed: 2,5mm22.T, J52.T
unnamed: 2,5mm23.R, J40.2, J43.2
unnamed: 2,5mm23.S, J40.3, J43.3, J47.S
unnamed: 2,5mm23.T, J40.T, J43.T, R45.2
unnamed: C93.1, J46.V, MK23.1 (-), R47.1
unnamed: C112.1, D46.2 (A), J46.W, SW41.2
unnamed: D46.1 (K), R47.2
unnamed: J41.2, J42.2, J50.V
unnamed: J41.3, J42.3, J50.W
unnamed: J41.T, J42.T, J50.U
unnamed: J44.R, J44.T, R46.1
unnamed: J44.S, J45.S
unnamed: J45.R, J45.T, R46.2
unnamed: J47.R, J47.T, R45.1
unnamed: J52.TN, LS24.1

Notes on the sheet:
S gn GND
Handset
Version B
Kenwood Programming Cable
3,5 mm PC Audio IN
Radio
T ws SPK+
USB2SER Connection
W sw PTT
V rt +MIC
Version A
