trygvis/Quansheng_UV-K5_Wiki/hardware/KiCad/UVK5_reversing_06-02-2024/Keypad.kicad_sch

## KiCad design hardware/KiCad/UVK5_reversing_06-02-2024/Keypad.kicad_sch (2024-02-06)

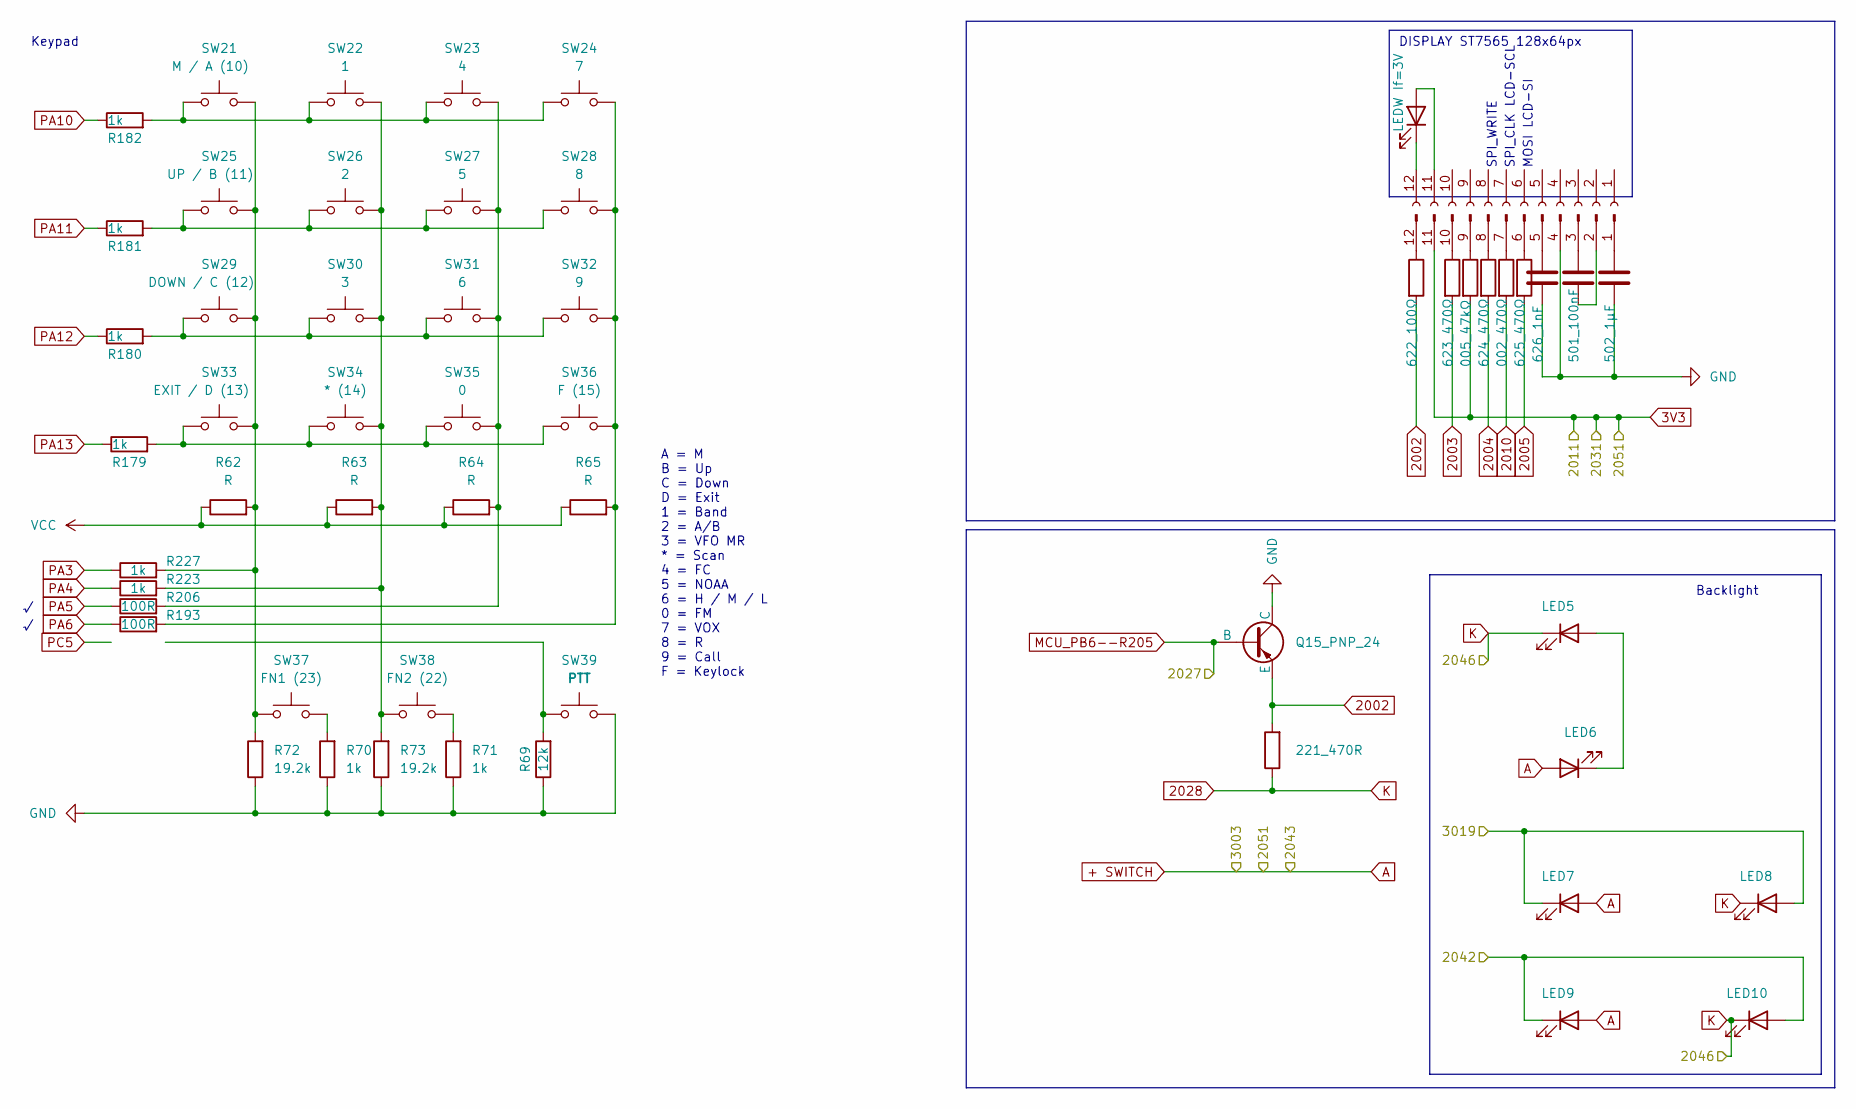
[picture p96: schematic Keypad.kicad_sch]

Parts:
C73: 626_1nF
C124: 501_100nF
C125: 502_1µF
D48: LED5
D49: LED6
D50: LED7
D51: LED9
D52: LED8
D53: LED10
D59: LEDW If=3V
J39: Conn_01x12_Socket
J53: Conn_01x12_Pin
Q15: Q15_PNP_24
R62, R63, R64, R65: R
R69: 12k
R70, R71, R179, R180, R181, R182, R223, R227: 1k
R72, R73: 19.2k
R84: 622_100Ω
R86: 623_470Ω
R87: 005_47kΩ
R88: 624_470Ω
R89: 625_470Ω
R90: 002_470Ω
R193, R206: 100R
R221: 221_470R
SW21: M / A (10)
SW22: 1
SW23: 4
SW24: 7
SW25: UP / B (11)
SW26: 2
SW27: 5
SW28: 8
SW29: DOWN / C (12)
SW30: 3
SW31: 6
SW32: 9
SW33: EXIT / D (13)
SW34: * (14)
SW35: 0
SW36: F (15)
SW37: FN1 (23)
SW38: FN2 (22)
SW39: PTT

Connections:
2002: Q15.3 (E), R84.2, R221.2
2003: R86.2
2004: R88.2
2005: R89.2
2010: R90.2
2028: D48.1 (K), D52.1 (K), D53.1 (K), R221.1
2042: D51.1 (K), D53.2 (A)
3019: D50.1 (K), D52.2 (A)
+ SWITCH: D49.2 (A), D50.2 (A), D51.2 (A), J53.11, R87.2
GND: C73.2, C125.2, J53.4, Q15.1 (C), R69.1, R70.1, R71.1, R72.1, R73.1, SW39.2
MCU_PB6--R205: Q15.2 (B)
unnamed: C73.1, J53.5
unnamed: C124.1, J53.3
unnamed: C124.2, J53.2
unnamed: C125.1, J53.1
unnamed: D48.2 (A), D49.1 (K)
unnamed: D59.1 (K), J39.12
unnamed: D59.2 (A), J39.11
unnamed: J53.6, R89.1
unnamed: J53.7, R90.1
unnamed: J53.8, R88.1
unnamed: J53.9, R87.1
unnamed: J53.10, R86.1
unnamed: J53.12, R84.1
unnamed: R69.2, SW39.1
unnamed: R70.2, SW37.2
unnamed: R71.2, SW38.2
unnamed: R179.2, SW33.1, SW34.1, SW35.1, SW36.1
unnamed: R180.2, SW29.1, SW30.1, SW31.1, SW32.1
unnamed: R181.2, SW25.1, SW26.1, SW27.1, SW28.1
unnamed: R182.2, SW21.1, SW22.1, SW23.1, SW24.1
unnamed: R65.2, R193.2, SW24.2, SW28.2, SW32.2, SW36.2
unnamed: R64.2, R206.2, SW23.2, SW27.2, SW31.2, SW35.2
unnamed: R63.2, R73.2, R223.2, SW22.2, SW26.2, SW30.2, SW34.2, SW38.1
unnamed: R62.2, R72.2, R227.2, SW21.2, SW25.2, SW29.2, SW33.2, SW37.1
PA3: R227.1
PA4: R223.1
PA5: R206.1
PA6: R193.1
PA10: R182.1
PA11: R181.1
PA12: R180.1
PA13: R179.1
VCC: R62.1, R63.1, R64.1, R65.1

Notes on the sheet:
Keypad
A = M B = Up C = Down D = Exit 1 = Band 2 = A/B 3 = VFO MR * = Scan 4 = FC 5 = NOAA 6 = H / M / L 0 = FM 7 = VOX 8 = R 9 = Call F = Keylock
SPI_WRITE
MOSI LCD-SI
Backlight
DISPLAY ST7565 128x64px
SPI_CLK LCD-SCL
