trygvis/Quansheng_UV-K5_Wiki/hardware/KiCad/UVK5_reversing_06-02-2024/Logic.kicad_sch

## KiCad design hardware/KiCad/UVK5_reversing_06-02-2024/Logic.kicad_sch (2024-02-06)

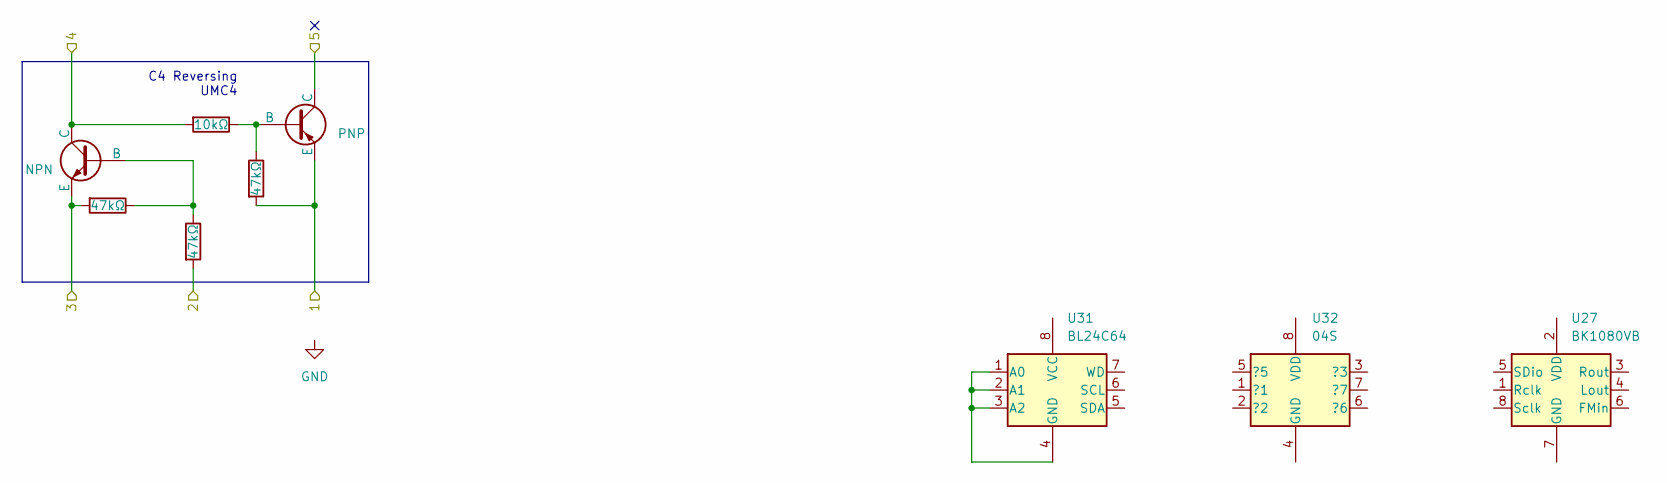
[picture p97: schematic Logic.kicad_sch]

Parts:
Q37: NPN
Q38: PNP
R102, R103, R104: 47kΩ
R107: 10kΩ
U27: BK1080VB; SOP-8_3.9x4.9mm_P1.27mm
U31: BL24C64; SOP-8_3.9x4.9mm_P1.27mm
U32: 04S; TSSOP-8_4.4x3mm_P0.65mm

Connections:
1: Q38.3 (E), R102.2
2: R103.2
3: Q37.3 (E), R104.2
4: Q37.1 (C), R107.2
5: Q38.1 (C)
unnamed: Q37.2 (B), R103.1, R104.1
unnamed: Q38.2 (B), R102.1, R107.1
unnamed: U31.1 (A0), U31.2 (A1), U31.3 (A2), U31.4 (GND)

Notes on the sheet:
C4 Reversing UMC4
