trygvis/Quansheng_UV-K5_Wiki/hardware/KiCad/UVK5_reversing_06-02-2024/RX_path_sch.kicad_sch

## KiCad design hardware/KiCad/UVK5_reversing_06-02-2024/RX_path_sch.kicad_sch (2024-02-06)

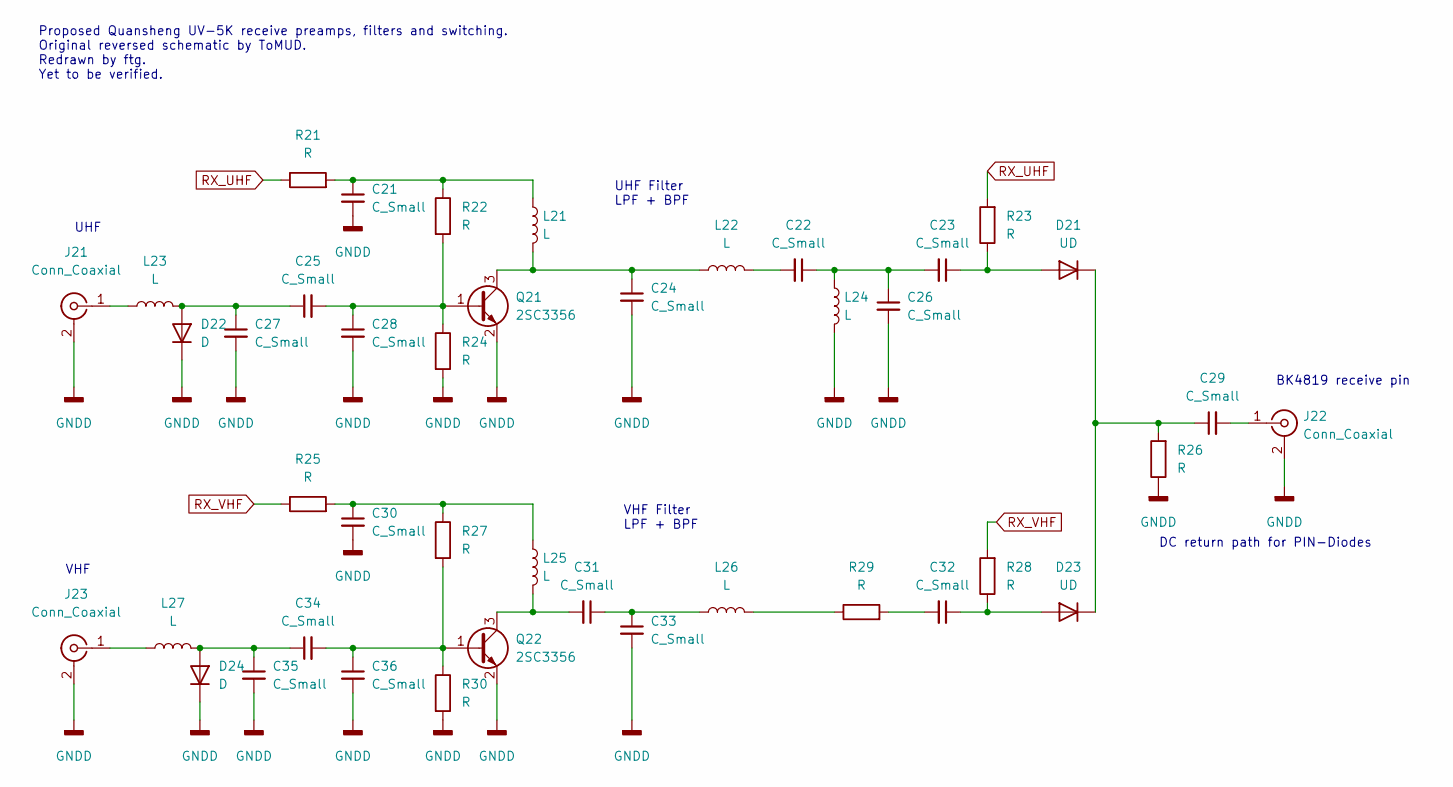
[picture p98: schematic RX_path_sch.kicad_sch]

Parts:
C21, C22, C23, C24, C25, C26, C27, C28, C29, C30, C31, C32, C33, C34, C35, C36: C_Small
D21, D23: UD
D22, D24: D
J21, J22, J23: Conn_Coaxial
L21, L22, L23, L24, L25, L26, L27: L
Q21, Q22: 2SC3356; SOT-323_SC-70
R21, R22, R23, R24, R25, R26, R27, R28, R29, R30: R

Connections:
GNDD: C21.2, C24.2, C26.2, C27.2, C28.2, C30.2, C33.2, C35.2, C36.2, D22.1 (K), D24.1 (K), J21.2 (Ext), J22.2 (Ext), J23.2 (Ext), L24.2, Q21.2 (E), Q22.2 (E), R24.2, R26.1, R30.2
unnamed: C21.1, L21.1, R21.2, R22.1
unnamed: C22.1, C23.2, C26.1, L24.1
unnamed: C22.2, L22.2
unnamed: C23.1, D21.2 (A), R23.1
unnamed: C24.1, L21.2, L22.1, Q21.3 (C)
unnamed: C25.1, C27.1, D22.2 (A), L23.2
unnamed: C25.2, C28.1, Q21.1 (B), R22.2, R24.1
unnamed: C29.1, D21.1 (K), D23.1 (K), R26.2
unnamed: C29.2, J22.1 (In)
unnamed: C30.1, L25.1, R25.2, R27.1
unnamed: C31.1, C33.1, L26.1
unnamed: C31.2, L25.2, Q22.3 (C)
unnamed: C32.1, D23.2 (A), R28.1
unnamed: C32.2, R29.2
unnamed: C34.1, C35.1, D24.2 (A), L27.2
unnamed: C34.2, C36.1, Q22.1 (B), R27.2, R30.1
unnamed: J21.1 (In), L23.1
unnamed: J23.1 (In), L27.1
unnamed: L26.2, R29.1
RX_UHF: R21.1, R23.2
RX_VHF: R25.1, R28.2

Notes on the sheet:
BK4819 receive pin
UHF Filter LPF + BPF
VHF
UHF
DC return path for PIN-Diodes
Proposed Quansheng UV-5K receive preamps, filters and switching. Original reversed schematic by ToMUD. Redrawn by ftg. Yet to be verified.
VHF Filter LPF + BPF
