trygvis/Quansheng_UV-K5_Wiki/hardware/KiCad/UVK5_reversing_06-02-2024/TX_chain_sch.kicad_sch

## KiCad design hardware/KiCad/UVK5_reversing_06-02-2024/TX_chain_sch.kicad_sch (2024-02-06)

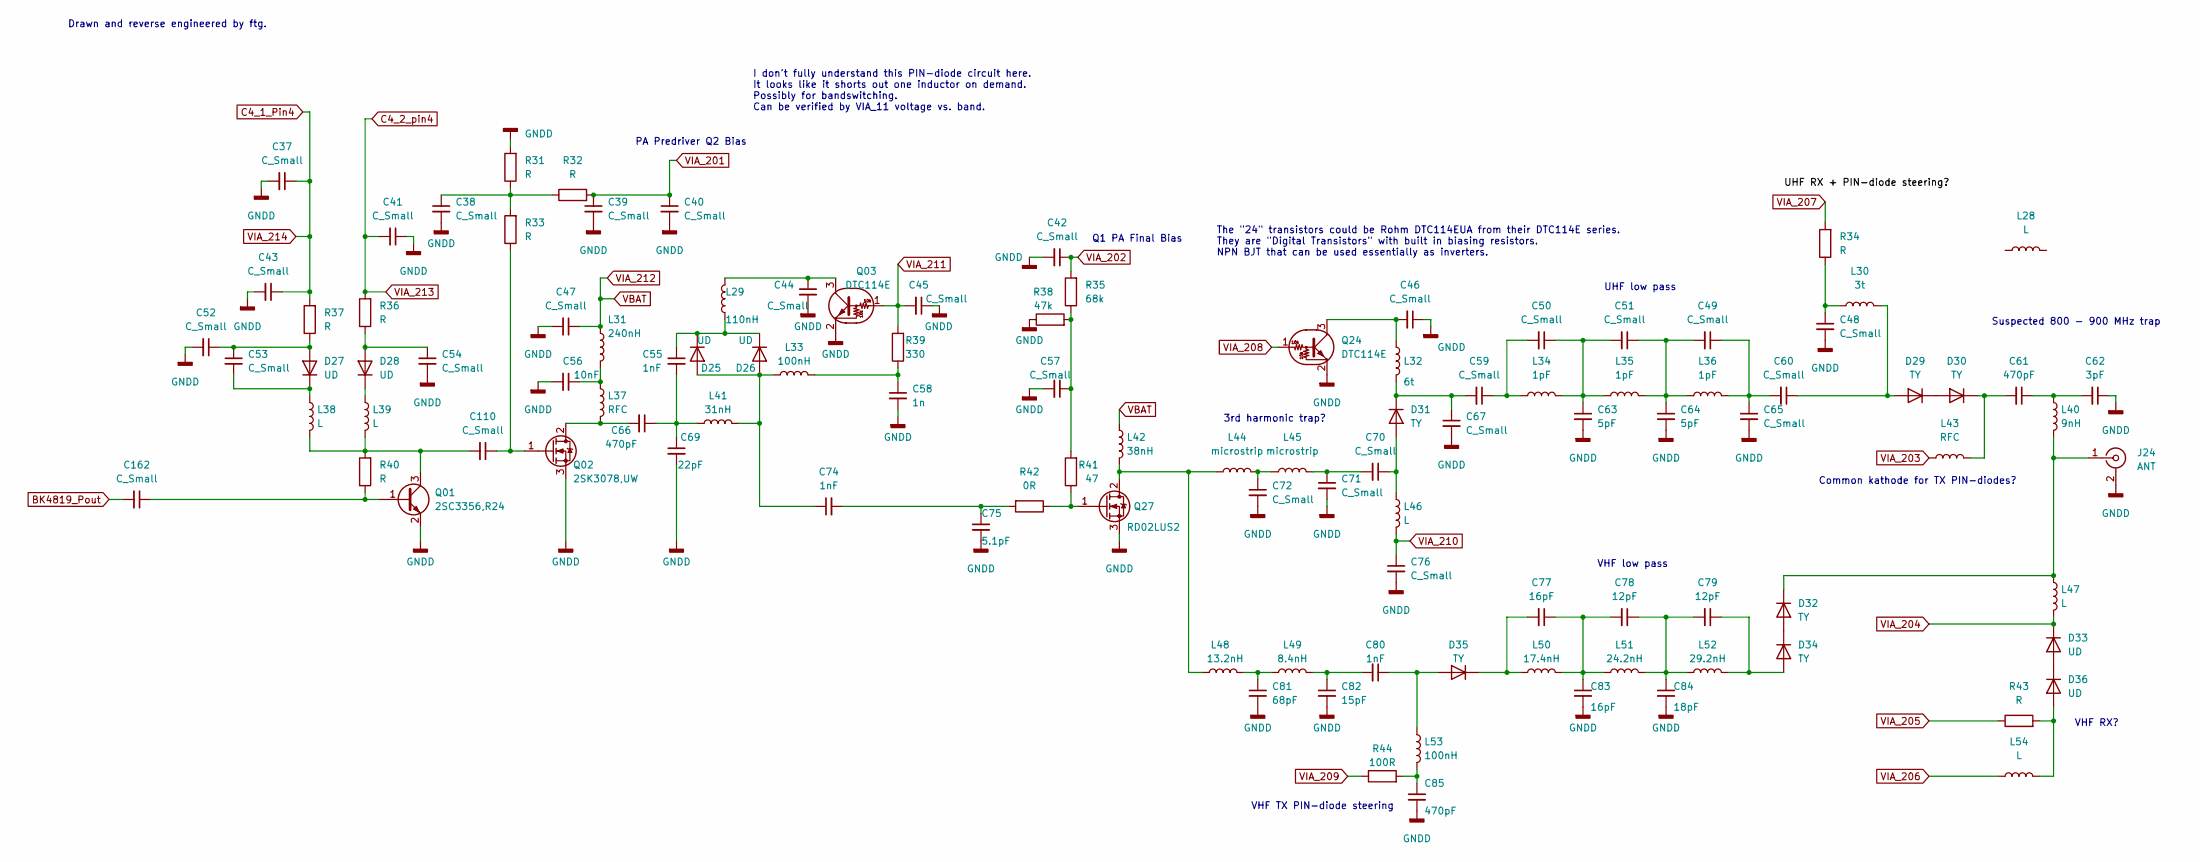
[picture p99: schematic TX_chain_sch.kicad_sch]

Parts:
C37, C38, C39, C40, C41, C42, C43, C44, C45, C46, C47, C48, C49, C50, C51, C52, C53, C54, C57, C59, C60, C65, C67, C70, C71, C72, C76, C110, C162: C_Small
C55, C74, C80: 1nF
C56: 10nF
C58: 1n
C61, C66, C85: 470pF
C62: 3pF
C63, C64: 5pF
C69: 22pF
C75: 5.1pF
C77, C83: 16pF
C78, C79: 12pF
C81: 68pF
C82: 15pF
C84: 18pF
D25, D26, D27, D28, D33, D36: UD
D29, D30, D31, D32, D34, D35: TY
J24: ANT
L28, L38, L39, L46, L47, L54: L
L29: 110nH
L30: 3t
L31: 240nH
L32: 6t
L33, L53: 100nH
L34, L35, L36: 1pF
L37, L43: RFC
L40: 9nH
L41: 31nH
L42: 38nH
L44, L45: microstrip
L48: 13.2nH
L49: 8.4nH
L50: 17.4nH
L51: 24.2nH
L52: 29.2nH
Q01: 2SC3356,R24; SOT-323_SC-70
Q02: 2SK3078,UW; TO-220-3_Vertical
Q03, Q24: DTC114E
Q27: RD02LUS2; TO-220-3_Vertical
R31, R32, R33, R34, R36, R37, R40, R43: R
R35: 68k
R38: 47k
R39: 330
R41: 47
R42: 0R
R44: 100R

Connections:
BK4819_Pout: C162.2
C4_1_Pin4: C37.1, C43.1, R37.2
C4_2_pin4: C41.2, R36.2
GNDD: C37.2, C38.2, C39.2, C40.2, C41.1, C42.2, C43.2, C44.2, C45.1, C46.1, C47.2, C48.2, C52.2, C54.2, C56.2, C57.2, C58.2, C62.1, C63.2, C64.2, C65.2, C67.2, C69.2, C71.2, C72.2, C75.2, C76.2, C81.2, C82.2, C83.2, C84.2, C85.2, J24.2 (Ext), Q01.2 (E), Q02.3 (S), Q03.2 (E), Q24.2 (E), Q27.3 (S), R31.2, R38.1
unnamed: C38.1, R31.1, R32.1, R33.2
unnamed: C44.1, L29.2, Q03.3 (C)
unnamed: C46.2, L32.1, Q24.3 (C)
unnamed: C48.1, L30.1, R34.1
unnamed: C49.1, C60.2, C65.1, L36.2
unnamed: C49.2, C51.1, C64.1, L35.2, L36.1
unnamed: C50.1, C51.2, C63.1, L34.2, L35.1
unnamed: C50.2, C59.1, L34.1
unnamed: C52.1, C53.1, D27.2 (A), R37.1
unnamed: C53.2, D27.1 (K), L38.1
unnamed: C54.1, D28.2 (A), R36.1
unnamed: C55.1, D25.1 (K), D26.1 (K), L29.1
unnamed: C55.2, C66.1, C69.1, L41.1
unnamed: C56.1, L31.2, L37.1
unnamed: C57.1, R35.1, R38.2, R41.2
unnamed: C58.1, L33.2, R39.1
unnamed: C59.2, C67.1, D31.1 (K), L32.2
unnamed: C60.1, D29.2 (A), L30.2
unnamed: C61.1, C62.2, L40.1
unnamed: C61.2, D30.1 (K), L43.2
unnamed: C66.2, L37.2, Q02.2 (D)
unnamed: C70.1, D31.2 (A), L46.1
unnamed: C70.2, C71.1, L45.2
unnamed: C72.1, L44.2, L45.1
unnamed: C74.1, D25.2 (A), D26.2 (A), L33.1, L41.2
unnamed: C74.2, C75.1, R42.2
unnamed: C77.1, C78.2, C83.1, L50.2, L51.1
unnamed: C77.2, D35.1 (K), L50.1
unnamed: C78.1, C79.2, C84.1, L51.2, L52.1
unnamed: C79.1, D34.2 (A), L52.2
unnamed: C80.1, D35.2 (A), L53.1
unnamed: C80.2, C82.1, L49.2
unnamed: C81.1, L48.2, L49.1
unnamed: C85.1, L53.2, R44.2
unnamed: C110.1, Q02.1 (G), R33.1
unnamed: C110.2, L38.2, L39.2, Q01.3 (C), R40.2
unnamed: C162.1, Q01.1 (B), R40.1
unnamed: D28.1 (K), L39.1
unnamed: D29.1 (K), D30.2 (A)
unnamed: D32.1 (K), J24.1 (In), L40.2, L47.1
unnamed: D32.2 (A), D34.1 (K)
unnamed: D33.2 (A), D36.1 (K)
unnamed: D36.2 (A), L54.2, R43.2
unnamed: L42.2, L44.1, L48.1, Q27.2 (D)
unnamed: Q27.1 (G), R41.1, R42.1
VBAT: C47.1, L31.1, L42.1
VIA_201: C39.1, C40.1, R32.2
VIA_202: C42.1, R35.2
VIA_203: L43.1
VIA_204: D33.1 (K), L47.2
VIA_205: R43.1
VIA_206: L54.1
VIA_207: R34.2
VIA_208: Q24.1 (B)
VIA_209: R44.1
VIA_210: C76.1, L46.2
VIA_211: C45.2, Q03.1 (B), R39.2

Notes on the sheet:
VHF low pass
The "24" transistors could be Rohm DTC114EUA from their DTC114E series. They are "Digital Transistors" with built in biasing resistors. NPN BJT that can be used essentially as inverters.
PA Predriver Q2 Bias
Drawn and reverse engineered by ftg.
VHF RX?
UHF low pass
Suspected 800 - 900 MHz trap
Common kathode for TX PIN-diodes?
Q1 PA Final Bias
I don't fully understand this PIN-diode circuit here. It looks like it shorts out one inductor on demand. Possibly for bandswitching. Can be verified by VIA_11 voltage vs. band.
3rd harmonic trap?
VHF TX PIN-diode steering
