trygvis/Quansheng_UV-K5_Wiki/hardware/KiCad/UVK5_reversing_06-02-2024/USB2SERIAL.kicad_sch

## KiCad design hardware/KiCad/UVK5_reversing_06-02-2024/USB2SERIAL.kicad_sch (2024-02-06)

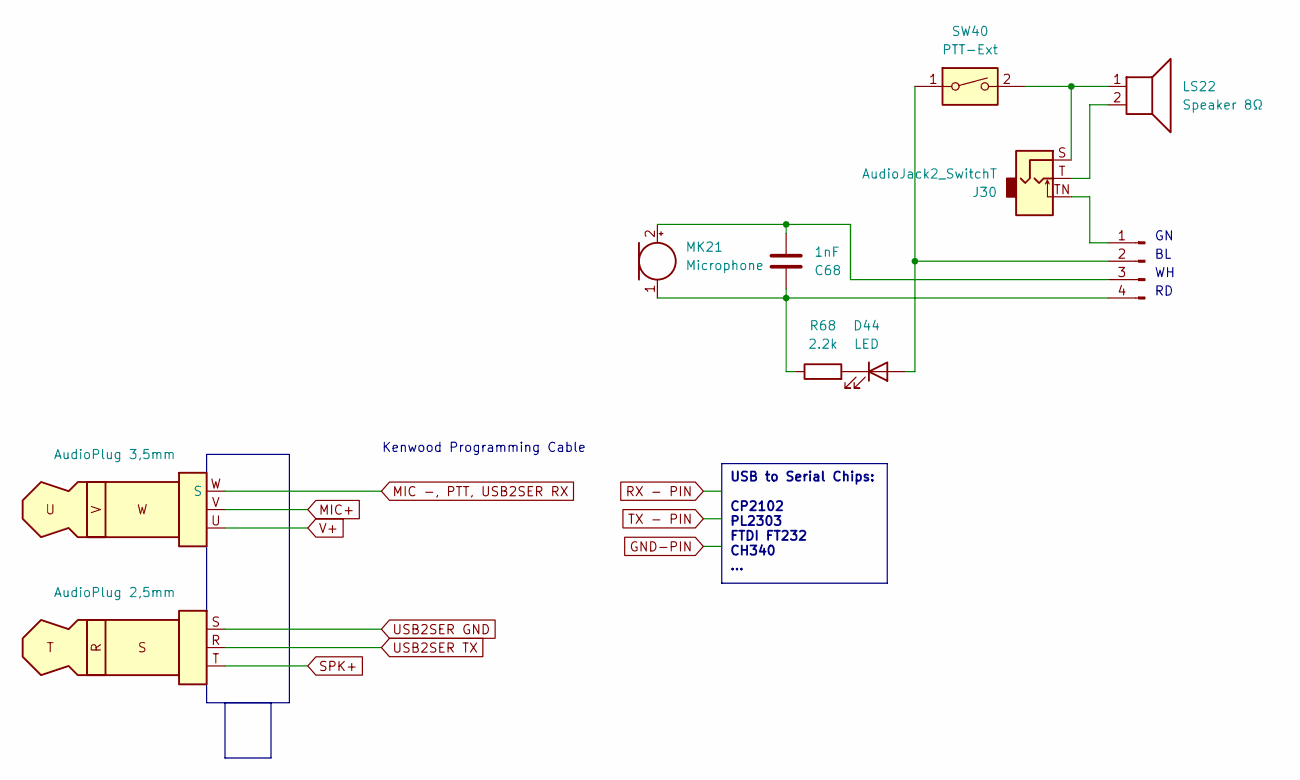
[picture p100: schematic USB2SERIAL.kicad_sch]

Parts:
2,5mm21: AudioPlug 2,5mm
C68: 1nF
D44: LED
J30: AudioJack2_SwitchT
J31: Conn_01x04_Pin
J32: AudioPlug 3,5mm
LS22: Speaker 8Ω
MK21: Microphone
R68: 2.2k
SW40: PTT-Ext

Connections:
MIC -, PTT, USB2SER RX: J32.W (S)
MIC+: J32.V
unnamed: C68.1, J31.4, MK21.1 (-), R68.1
unnamed: C68.2, J31.3, MK21.2 (+)
unnamed: D44.1 (K), R68.2
unnamed: D44.2 (A), J31.2, SW40.1
unnamed: J30.S, LS22.1, SW40.2
unnamed: J30.T, LS22.2
unnamed: J30.TN, J31.1
SPK+: 2,5mm21.T
USB2SER GND: 2,5mm21.S
USB2SER TX: 2,5mm21.R
V+: J32.U

Notes on the sheet:
USB to Serial Chips: CP2102 PL2303 FTDI FT232 CH340 ...
Kenwood Programming Cable
