trygvis/Quansheng_UV-K5_Wiki/hardware/KiCad/UVK5_reversing_06-02-2024/audio.kicad_sch

## KiCad design hardware/KiCad/UVK5_reversing_06-02-2024/audio.kicad_sch (2024-02-06)

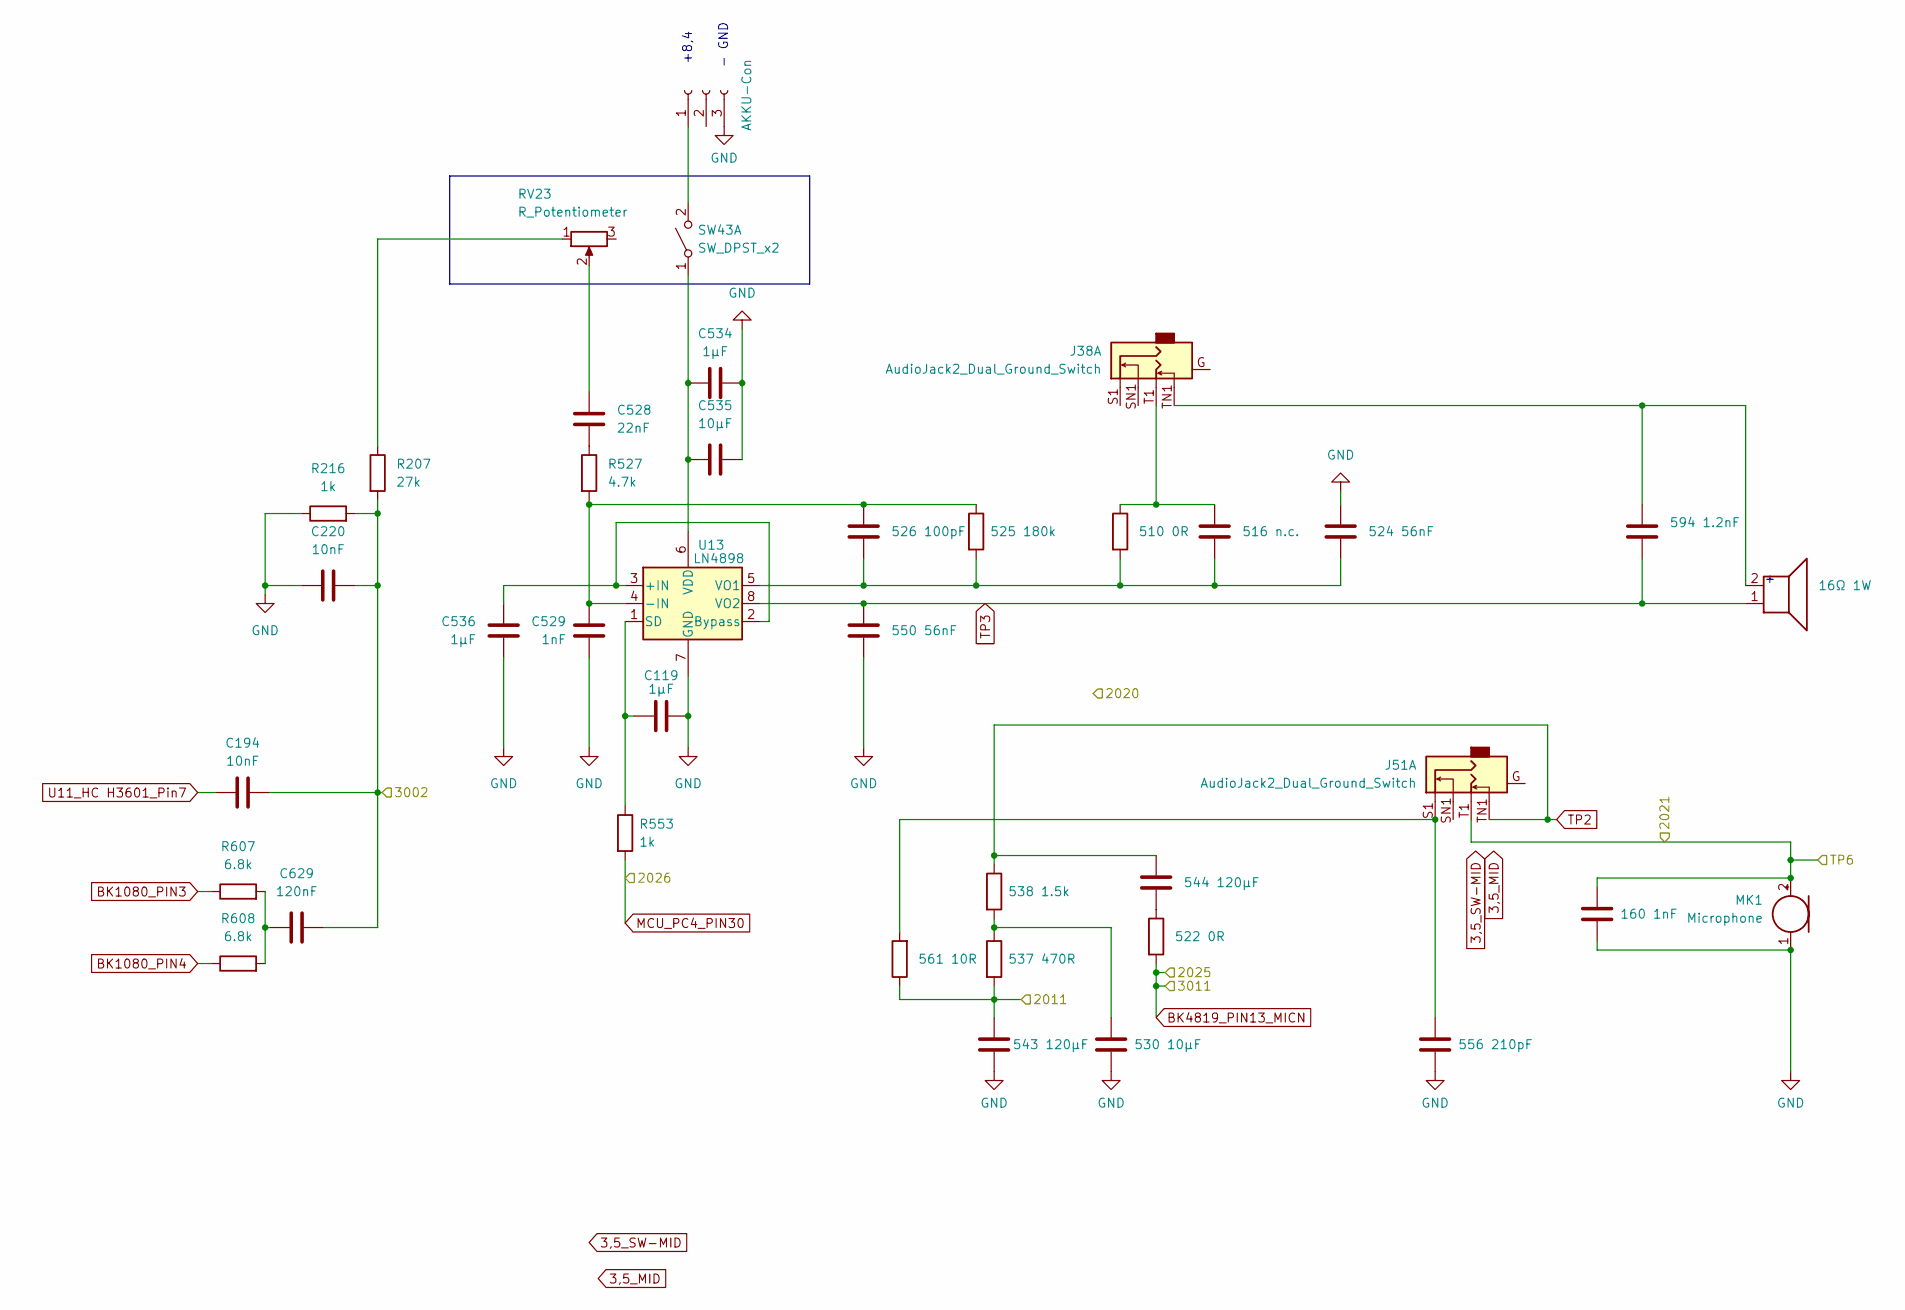
[picture p101: schematic audio.kicad_sch]

Parts:
C116: 544 120µF
C117: 594 1.2nF
C119, C534, C536: 1µF
C121: 530 10µF
C122: 543 120µF
C123: 556 210pF
C160: 160 1nF
C194, C220: 10nF
C516: 516 n.c.
C524: 524 56nF
C526: 526 100pF
C528: 22nF
C529: 1nF
C535: 10µF
C550: 550 56nF
C629: 120nF
J38, J51: AudioJack2_Dual_Ground_Switch
J49: AKKU-Con
LS1: 16Ω 1W
MK1: Microphone
R80: 538 1.5k
R81: 537 470R
R82: 522 0R
R83: 561 10R
R207: 27k
R216, R553: 1k
R510: 510 0R
R525: 525 180k
R527: 4.7k
R607, R608: 6.8k
RV23: R_Potentiometer
SW43: SW_DPST_x2
U13: LN4898; SOP-8_3.9x4.9mm_P1.27mm

Connections:
2011: C122.1, R81.2, R83.1
2021: C160.1, J51.T1, MK1.2 (+)
3002: C194.1, C220.1, C629.1, R207.2, R216.2
BK1080_PIN3: R607.1
BK1080_PIN4: R608.1
BK4819_PIN13_MICN: R82.2
GND: C119.1, C121.2, C122.2, C123.1, C160.2, C220.2, C524.1, C529.1, C534.1, C535.1, C536.2, C550.2, J49.3, MK1.1 (-), R216.1, U13.7 (GND)
MCU_PC4_PIN30: R553.2
unnamed: C116.2, R82.1
unnamed: C117.2, J38.TN1, LS1.2
unnamed: C119.2, R553.1, U13.1 (SD)
unnamed: C121.1, R80.2, R81.1
unnamed: C123.2, J51.S1, R83.2
unnamed: C516.1, J38.T1, R510.1
unnamed: C516.2, C524.2, C526.2, R510.2, R525.2, U13.5 (VO1)
unnamed: C526.1, C529.2, R525.1, R527.2, U13.4 (-IN)
unnamed: C528.1, R527.1
unnamed: C528.2, RV23.2
unnamed: C534.2, C535.2, SW43.1 (A), U13.6 (VDD)
unnamed: C536.1, U13.2 (Bypass), U13.3 (+IN)
unnamed: C629.2, R607.2, R608.2
unnamed: J49.1, SW43.2 (B)
unnamed: R207.1, RV23.1
TP2: C116.1, J51.TN1, R80.1
TP3: C117.1, C550.1, LS1.1, U13.8 (VO2)
U11_HC H3601_Pin7: C194.2

Notes on the sheet:
- GND
+8,4
