trygvis/Quansheng_UV-K5_Wiki/hardware/KiCad/UVK5_reversing_06-02-2024/led.kicad_sch

## KiCad design hardware/KiCad/UVK5_reversing_06-02-2024/led.kicad_sch (2024-02-06)

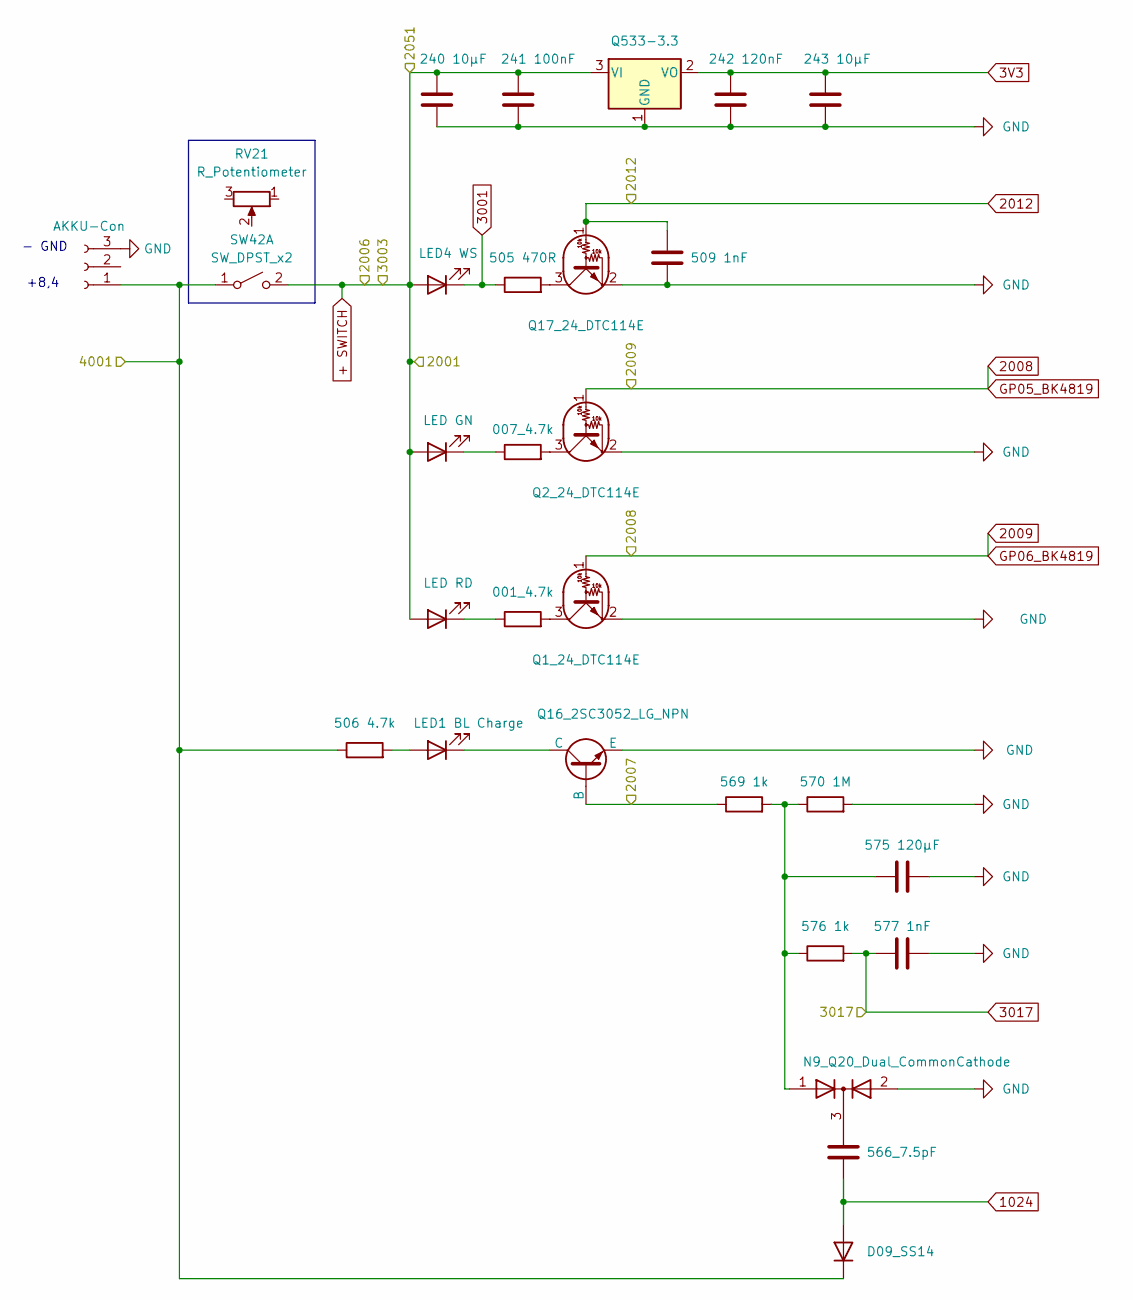
[picture p102: schematic led.kicad_sch]

Parts:
C88: 509 1nF
C114: 575 120µF
C115: 577 1nF
C240: 240 10µF
C241: 241 100nF
C242: 242 120nF
C243: 243 10µF
C566: 566_7.5pF
D45: LED4 WS
D55: LED GN
D56: LED RD
D57: LED1 BL Charge
D58: D09_SS14
D_Q21: N9_Q20_Dual_CommonCathode
J48: AKKU-Con
Q26: Q2_24_DTC114E
Q32: Q1_24_DTC114E
Q35: Q16_2SC3052_LG_NPN
Q39: Q17_24_DTC114E
R48: 505 470R
R49: 007_4.7k
R50: 001_4.7k
R51: 506 4.7k
R61: 569 1k
R74: 570 1M
R75: 576 1k
RV21: R_Potentiometer
SW42: SW_DPST_x2
U24: Q533-3.3

Connections:
3V3: C242.2, C243.2, U24.2 (VO)
1024: C566.2, D58.2 (A)
2007: Q35.2 (B), R61.1
2008: Q26.1 (B)
2009: Q32.1 (B)
2012: C88.2, Q39.1 (B)
3001: D45.1 (K), R48.1
3017: C115.1, R75.2
4001: D58.1 (K), J48.1, R51.1, SW42.1 (A)
+ SWITCH: C240.2, C241.2, D45.2 (A), D55.2 (A), D56.2 (A), SW42.2 (B), U24.3 (VI)
GND: C88.1, C114.2, C115.2, C240.1, C241.1, C242.1, C243.1, D_Q21.2 (A), J48.3, Q26.2 (E), Q32.2 (E), Q35.3 (E), Q39.2 (E), R74.2, U24.1 (GND)
unnamed: C114.1, D_Q21.1 (A), R61.2, R74.1, R75.1
unnamed: C566.1, D_Q21.3 (K)
unnamed: D55.1 (K), R49.1
unnamed: D56.1 (K), R50.1
unnamed: D57.1 (K), Q35.1 (C)
unnamed: D57.2 (A), R51.2
unnamed: Q26.3 (C), R49.2
unnamed: Q32.3 (C), R50.2
unnamed: Q39.3 (C), R48.2

Notes on the sheet:
- GND
+8,4
