trygvis/Quansheng_UV-K5_Wiki/hardware/KiCad/UVK5_reversing_06-02-2024/untitled.kicad_sch

## KiCad design hardware/KiCad/UVK5_reversing_06-02-2024/untitled.kicad_sch (2024-02-06)

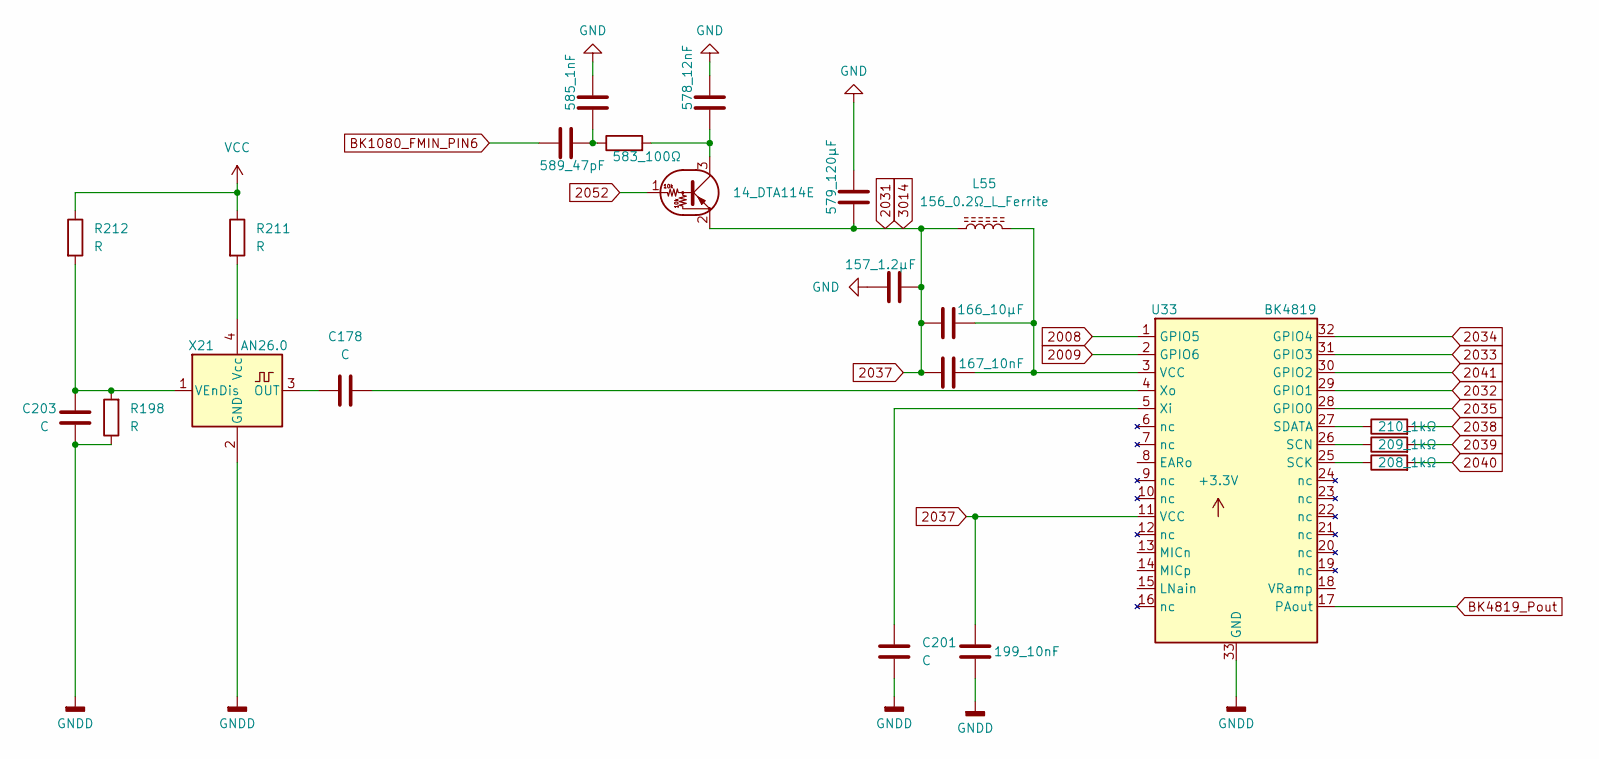
[picture p103: schematic untitled.kicad_sch]

Parts:
C129: 167_10nF
C132: 166_10µF
C133: 157_1.2µF
C134: 579_120µF
C135: 578_12nF
C136: 585_1nF
C139: 589_47pF
C178, C201, C203: C
C199: 199_10nF
L55: 156_0.2Ω_L_Ferrite
Q36: 14_DTA114E
R101: 583_100Ω
R198, R211, R212: R
R208: 208_1kΩ
R209: 209_1kΩ
R210: 210_1kΩ
U33: BK4819; LQFP-32_7x7mm_P0.8mm
X21: AN26.0; Oscillator_SMD_AN26.0-4Pin_5.0x3.2mm

Connections:
2008: U33.1 (GPIO5)
2009: U33.2 (GPIO6)
2031: C129.2, C132.2, C133.1, C134.2, C199.2, L55.1, Q36.2 (E), U33.11 (VCC)
2032: U33.29 (GPIO1)
2033: U33.31 (GPIO3)
2034: U33.32 (GPIO4)
2035: U33.28 (GPIO0)
2038: R210.2
2039: R209.2
2040: R208.2
2041: U33.30 (GPIO2)
2052: Q36.1 (B)
BK1080_FMIN_PIN6: C139.1
BK4819_Pout: U33.17 (PAout)
GND: C133.2, C134.1, C135.1, C136.1
GNDD: C199.1, C201.1, C203.1, R198.1, U33.33 (GND)
unnamed: C129.1, C132.1, L55.2, U33.3 (VCC)
unnamed: C135.2, Q36.3 (C), R101.2
unnamed: C136.2, C139.2, R101.1
unnamed: C178.1, X21.3 (OUT)
unnamed: C178.2, U33.4 (Xo)
unnamed: C201.2, U33.5 (Xi)
unnamed: C203.2, R198.2, R212.2, X21.1 (VEnDis)
unnamed: R208.1, U33.25 (SCK)
unnamed: R209.1, U33.26 (SCN)
unnamed: R210.1, U33.27 (SDATA)
VCC: R211.1, R212.1
